garyStofer/wifi_wx_station/Hardware/Wifi_WX_Station/SPICE/rc-rc.asc

AC1: voltage; SINE(0 5 1.720K 0 0 0 300)
C1: cap; 1µf; V=10 Irms=11.456 Rser=0.004 Lser=0
C2: cap; 0.1µf
C3: cap; 1µf
R1: res; 8.2k; pwr=0.125
R2: res; 26.1k
R3: res; 8.2k
R4: res; 6.8K
Named nets: 0, out, vin, tap
.tran 400ms
.meas vmax MAX v(out) From 0.14 to 0.15
Use "View/Spice Error Log" to view the results of the .meas directive , or Ctrl-L
.meas vtap MAX v(tap) From 0.14 to 0.150
R3 and C2 is on Base station PCB
