garyStofer/wifi_wx_station/Hardware/Wifi_WX_Station/WindDir_WE28_A.1/Spice/IWind_encoder.asc

R4: res; 24.3k
R5: res; 14.3k
R6: res; 150k
R8: res; 100k
U2: opamp
V1: voltage; PULSE(0.33 2.97 00.1ms 10ms 75ns 100us 5.6ms 1)
V2: voltage; 3.3
Named nets: 0
.LIB opamp.sub
.tran 12ms
