garyStofer/wifi_wx_station/Hardware/Wifi_WX_Station/BMP085_HIH6130.brd

## EAGLE design Hardware/Wifi_WX_Station/BMP085_HIH6130.brd (2013-12-26)

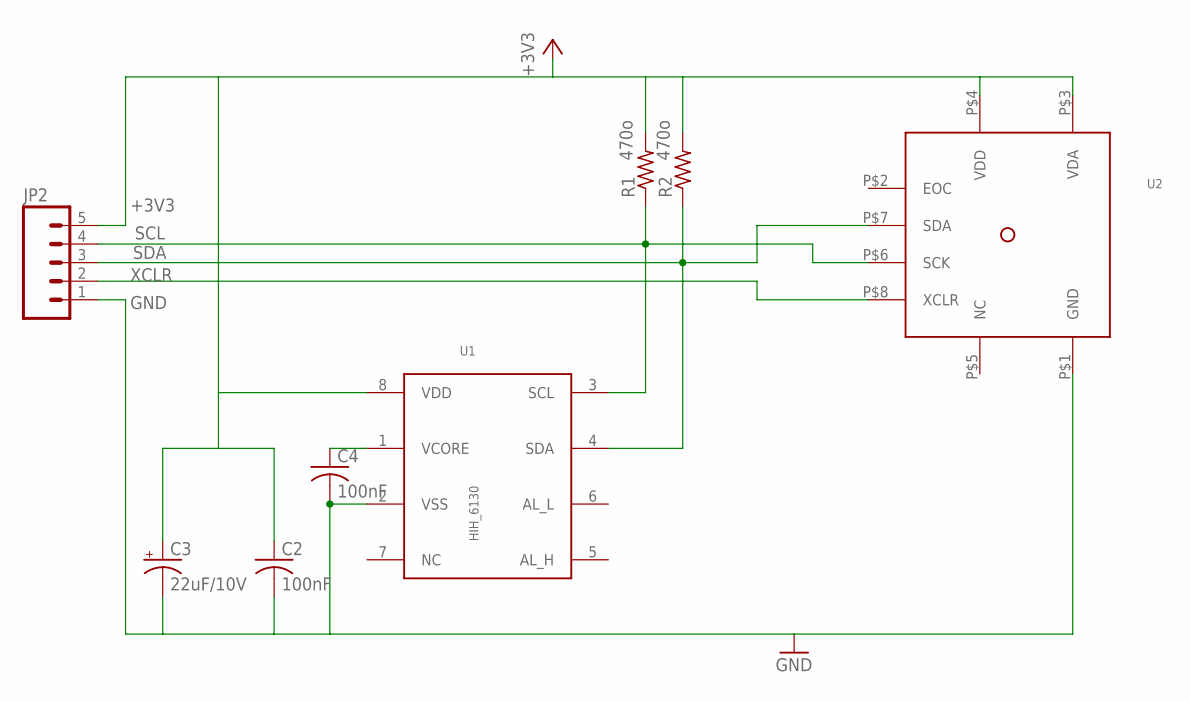
[picture p32: schematic BMP085_HIH6130.sch]

Parts:
C2, C4: 100nF; C0805K
C3: 22uF/10V; SMC_B
JP2: M05PTH; 1X05
R1, R2: 470o; R0603
U1: HIH_6130; SOIC8
U2: BMP085; LCC8

Connections:
+3V3: C2.1, C3.+, JP2.5, R1.2, R2.2, U1.8 (VDD), U2.P$3 (VDA), U2.P$4 (VDD)
GND: C2.2, C3.-, C4.2, JP2.1, U1.2 (VSS), U2.P$1 (GND)
unnamed: C4.1, U1.1 (VCORE)
SCL: JP2.4, R1.1, U1.3 (SCL), U2.P$6 (SCK)
SDA: JP2.3, R2.1, U1.4 (SDA), U2.P$7 (SDA)
XCLR: JP2.2, U2.P$8 (XCLR)

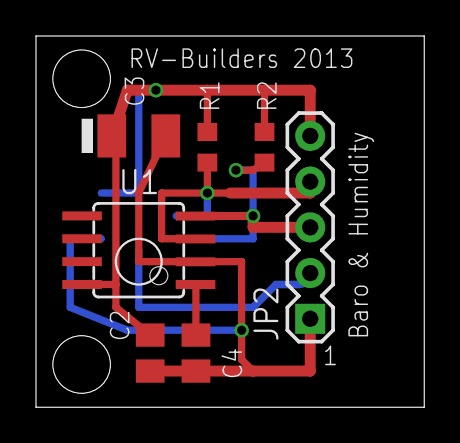
[picture p33: board BMP085_HIH6130.brd from above]

Board: 2 copper layers, 21.6 x 20.6 mm, 8 parts (1 on the bottom side), 6 nets.
