garyStofer/wifi_wx_station/Hardware/Wifi_WX_Station/Wind_enc.brd

## EAGLE design Hardware/Wifi_WX_Station/Wind_enc.brd (2013-11-12)

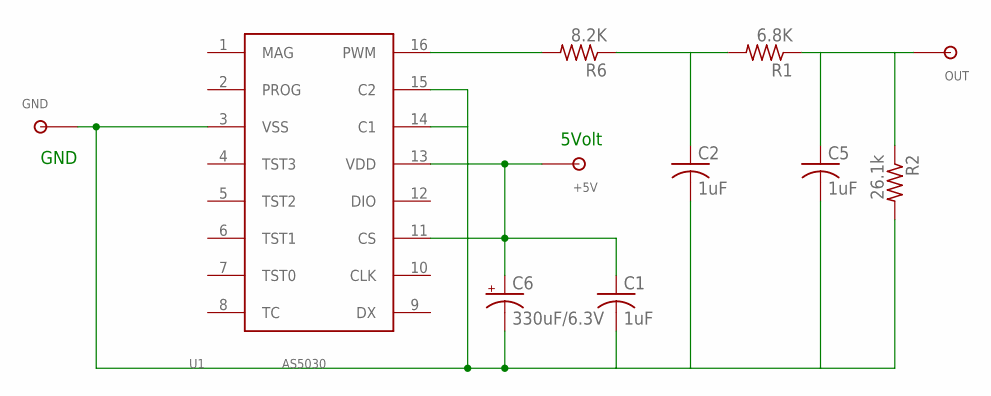
[picture p34: schematic Wind_enc.sch]

Parts:
+5V: TPSOL; TP_SOL
C1, C2, C5: 1uF; C0805K
C6: 330uF/6.3V; SMC_D
GND: TPSOL; TP_SOL
OUT: TPSOL; TP_SOL
R1: 6.8K; R0603
R2: 26.1k; R0603
R6: 8.2K; R0603
U1: AS5030; TSSOP16

Connections:
unnamed: +5V.P$1, C1.1, C6.+, U1.11 (CS), U1.13 (VDD)
unnamed: C1.2, C2.2, C5.2, C6.-, GND.P$1, R2.2, U1.3 (VSS), U1.14 (C1), U1.15 (C2)
unnamed: C5.1, OUT.P$1, R1.1, R2.1
unnamed: C2.1, R1.2, R6.1
unnamed: R6.2, U1.16 (PWM)

Notes on the sheet:
5Volt
GND

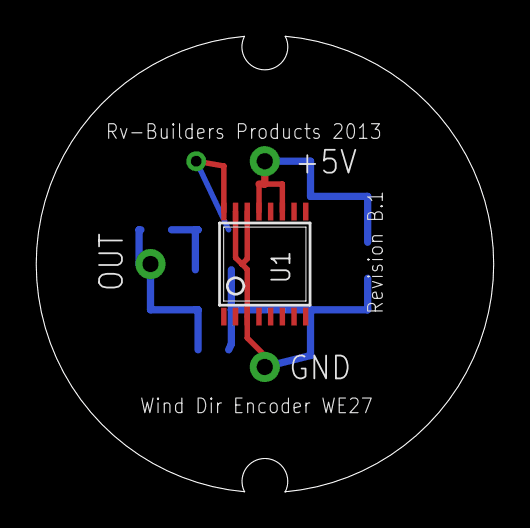
[picture p35: board Wind_enc.brd from above]

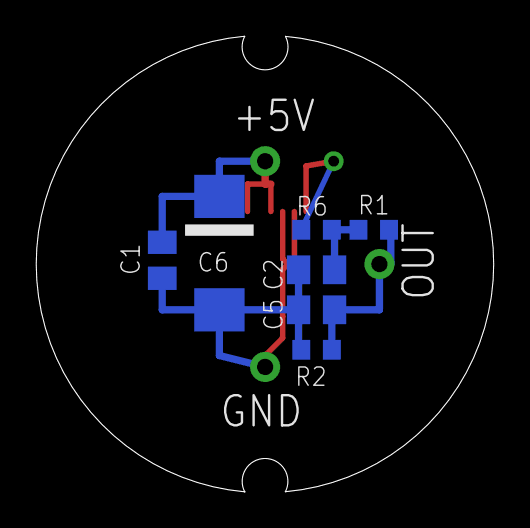
[picture p36: board Wind_enc.brd from below]

Board: 2 copper layers, 25.4 x 25.3 mm, 11 parts (7 on the bottom side), 5 nets.
