garyStofer/wifi_wx_station/Hardware/Wifi_WX_Station/VPower_feed.brd

## EAGLE design Hardware/Wifi_WX_Station/VPower_feed.brd (2013-03-08)

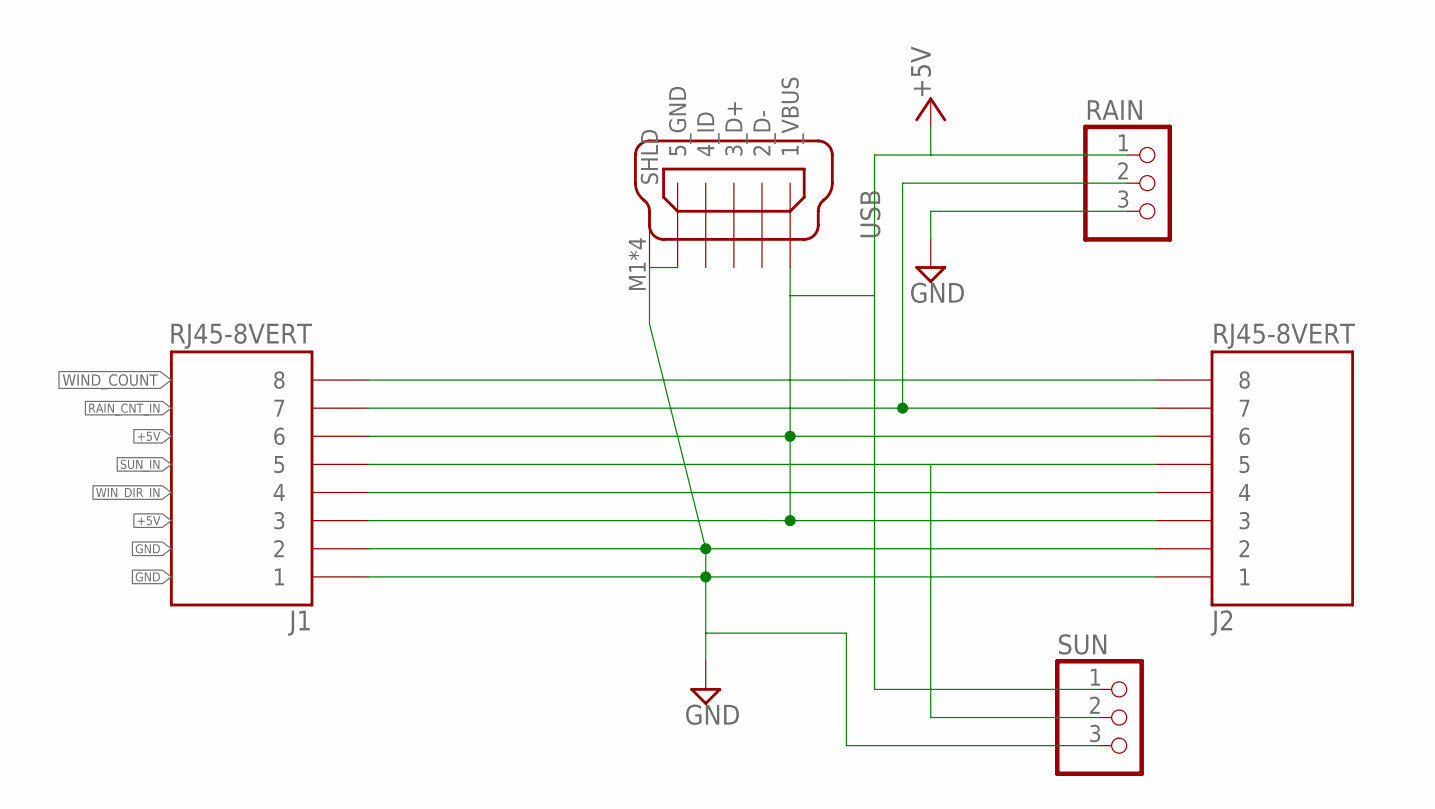
[picture p37: schematic VPower_feed.sch]

Parts:
J1, J2: RJ45-8VERT; RJ45_VERT
RAIN: PINHD-1X3MOLEX_KK; 1X3_MOLEX_KK
SUN: PINHD-1X3MOLEX_KK; 1X3_MOLEX_KK
USB: MINI-USB-32005-301; 32005-301

Connections:
+5V: J1.P$3 (3), J1.P$6 (6), J2.P$3 (3), J2.P$6 (6), RAIN.1, SUN.1, USB.1_VBUS
GND: J1.P$1 (1), J1.P$2 (2), J2.P$1 (1), J2.P$2 (2), RAIN.3, SUN.3, USB.5_USB_GND (5_GND), USB.M1 (SHLD), USB.M2 (SHLD), USB.M3 (SHLD), USB.M4 (SHLD)
RAIN_CNT_IN: J1.P$7 (7), J2.P$7 (7), RAIN.2
SUN_IN: J1.P$5 (5), J2.P$5 (5), SUN.2
WIND_COUNT: J1.P$8 (8), J2.P$8 (8)
WIN_DIR_IN: J1.P$4 (4), J2.P$4 (4)

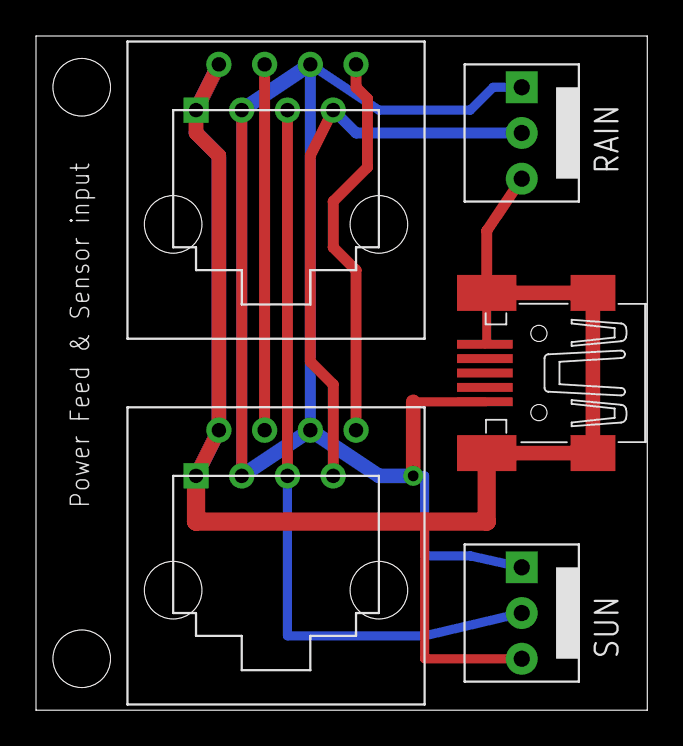
[picture p38: board VPower_feed.brd from above]

Board: 2 copper layers, 34.0 x 37.5 mm, 5 parts (0 on the bottom side), 6 nets.
