garyStofer/wifi_wx_station/Hardware/Wifi_WX_Station/sol_sens.brd

## EAGLE design Hardware/Wifi_WX_Station/sol_sens.brd (2013-03-08)

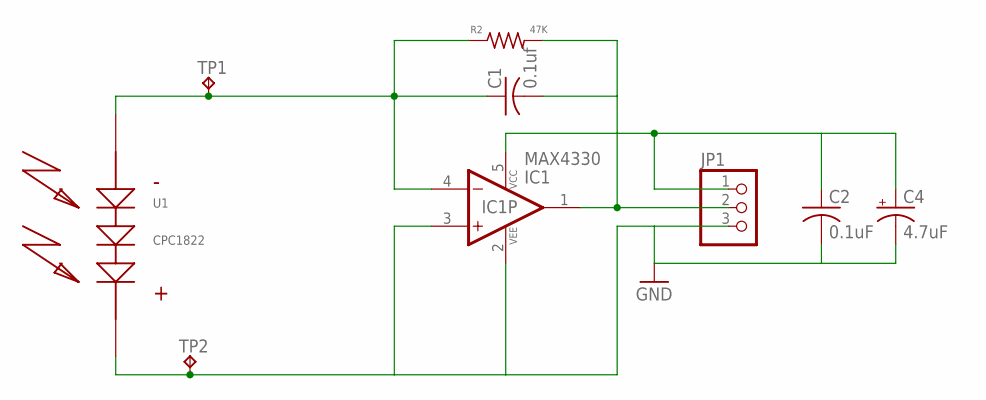
[picture p39: schematic sol_sens.sch]

Parts:
C1: 0.1uf; C0805
C2: 0.1uF; C0805
C4: 4.7uF; R/2012-12R
IC1: MAX4330; SOT23-5
JP1: PINHD-1X3; 1X03
R2: 47K; R0805
TP1, TP2: TPB1,27; B1,27
U1: CPC1822; SO08

Connections:
GND: C2.2, C4.-, IC1.2 (VEE), IC1.3 (+IN), JP1.3, TP2.PP, U1.8 (V+)
unnamed: C1.1, IC1.4 (-IN), R2.1, TP1.PP, U1.5 (V-)
unnamed: C1.2, IC1.1 (OUT), JP1.2, R2.2
unnamed: C2.1, C4.+, IC1.5 (VCC), JP1.1

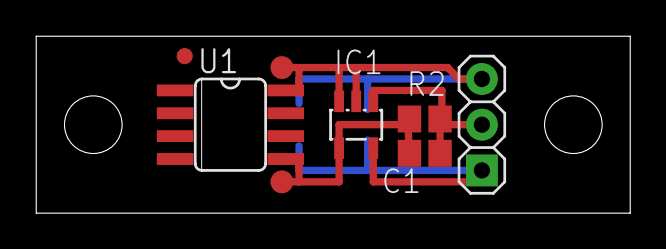
[picture p40: board sol_sens.brd from above]

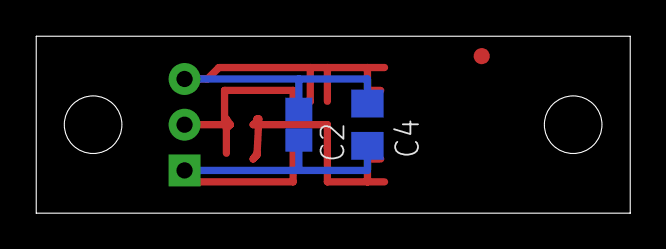
[picture p41: board sol_sens.brd from below]

Board: 2 copper layers, 33.0 x 9.8 mm, 9 parts (2 on the bottom side), 4 nets.
