garyStofer/wifi_wx_station/Hardware/Wifi_WX_Station/HP03S_HIH6130.brd

## EAGLE design Hardware/Wifi_WX_Station/HP03S_HIH6130.brd (2013-03-04)

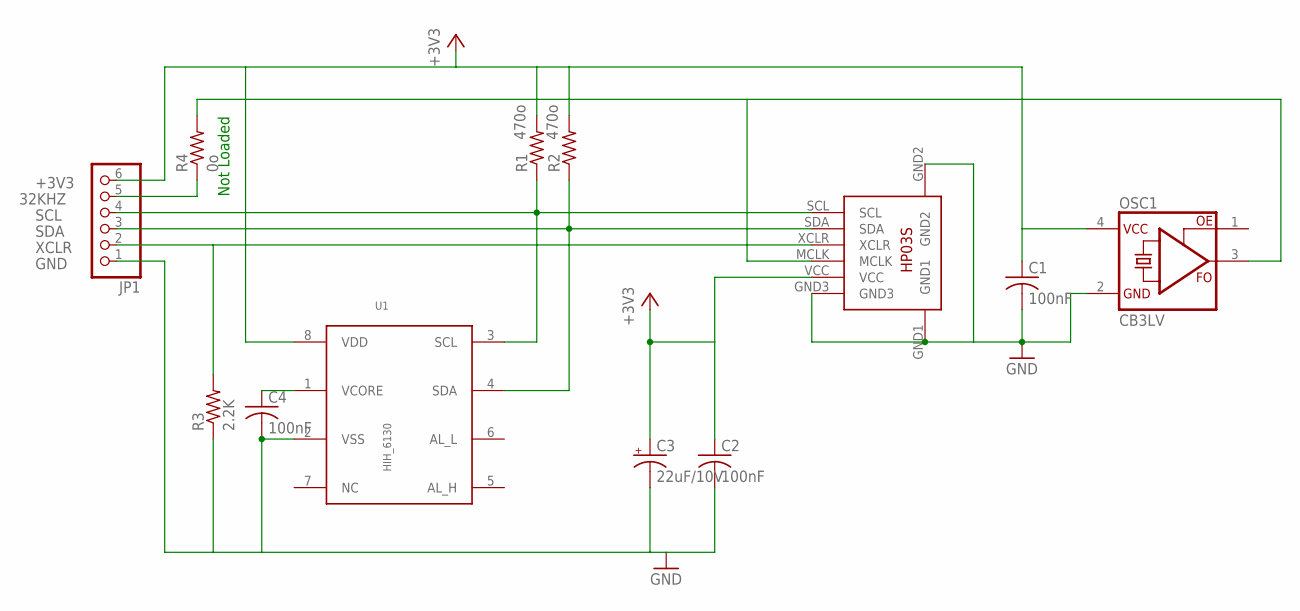
[picture p42: schematic HP03S_HIH6130.sch]

Parts:
C1: 100nF; C0805
C2, C4: 100nF; C0805K
C3: 22uF/10V; SMC_B
JP1: PINHD-1X6; 1X06
OSC1: CB3LV; SMD7.5X5MM
R1, R2: 470o; R0603
R3: 2.2K; R0603
R4: 0o; R0603
U1: HIH_6130; SOIC8
U2: HP03S

Connections:
32KHZ: JP1.5, R4.1
+3V3: C1.1, C2.1, C3.+, JP1.6, OSC1.4 (VCC), R1.2, R2.2, U1.8 (VDD), U2.VCC
GND: C1.2, C2.2, C3.-, C4.2, JP1.1, OSC1.2 (GND), R3.1, U1.2 (VSS), U2.GND1, U2.GND2, U2.GND3
unnamed: C4.1, U1.1 (VCORE)
RTCCLK: OSC1.3 (FO), R4.2, U2.MCLK
SCL: JP1.4, R1.1, U1.3 (SCL), U2.SCL
SDA: JP1.3, R2.1, U1.4 (SDA), U2.SDA
XCLR: JP1.2, R3.2, U2.XCLR

Notes on the sheet:
Not Loaded

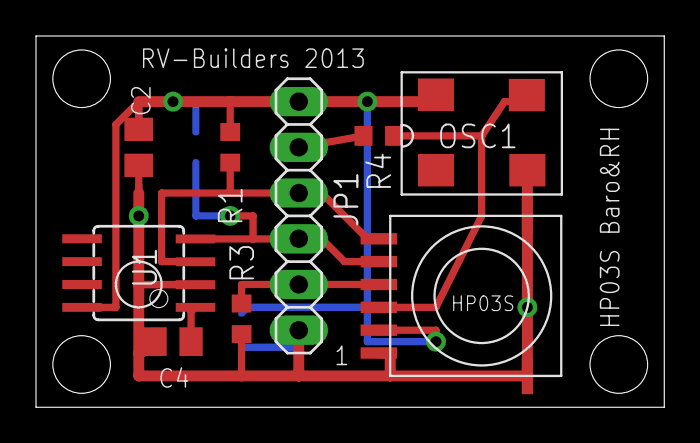
[picture p43: board HP03S_HIH6130.brd from above]

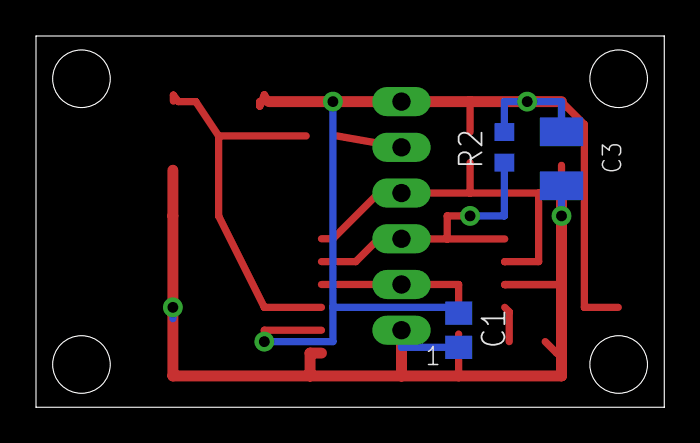
[picture p44: board HP03S_HIH6130.brd from below]

Board: 2 copper layers, 34.9 x 20.6 mm, 12 parts (3 on the bottom side), 8 nets.
