garyStofer/wifi_wx_station/Firmware/TCPIP/WiFi/WFMac_24G.c

/******************************************************************************

 MRF24W Driver Medium Access Control (MAC) Layer
 Module for Microchip TCP/IP Stack
  -Provides access to MRF24W WiFi controller
  -Reference: MRF24W Data sheet, IEEE 802.11 Standard

*******************************************************************************
 FileName:		WFMac.c
 Dependencies:	TCP/IP Stack header files
 Processor:		PIC18, PIC24F, PIC24H, dsPIC30F, dsPIC33F, PIC32
 Compiler:		Microchip C32 v1.10b or higher
				Microchip C30 v3.22 or higher
				Microchip C18 v3.34 or higher
 Company:		Microchip Technology, Inc.

 Software License Agreement

 Copyright (C) 2002-2010 Microchip Technology Inc.  All rights reserved.

 Microchip licenses to you the right to use, modify, copy, and distribute:
 (i)  the Software when embedded on a Microchip microcontroller or digital 
      signal controller product ("Device") which is integrated into 
      Licensee's product; or
 (ii) ONLY the Software driver source files ENC28J60.c, ENC28J60.h,
      ENCX24J600.c and ENCX24J600.h ported to a non-Microchip device used in 
	  conjunction with a Microchip ethernet controller for the sole purpose 
	  of interfacing with the ethernet controller.

 You should refer to the license agreement accompanying this Software for 
 additional information regarding your rights and obligations.

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

 Author				Date		Comment
~~~~~~~~~~~~~~~~~~~~~~~~~~~~~~~~~~~~~~~~~~~~~~~~~~~~~~~~~~~~~~~~~~~~~~~~~~~~~~~
 Michael Palladino	10/13/07	Original
 KO					31 Oct 2008	Port to PIC24F and PIC32 for TCP/IP stack v4.52
 KH					19 Jun 2009	Modified MACMemCopyAsync to support TCB to TCB copy
******************************************************************************/

/*
*********************************************************************************************************
*                                           INCLUDES                               
*********************************************************************************************************
*/

#include "TCPIP Stack/WFMac.h"

#if defined(WF_CS_TRIS) 

#include "TCPIP Stack/TCPIP.h"

#if defined( WF_CONSOLE )
#include "TCPIP Stack/WFConsole.h"
#include "IperfApp.h"
#endif 


#if defined(STACK_USE_UART)
extern void WF_OutputConnectionContext(void);
extern void ValidateConfig(void);
#endif

/*
*********************************************************************************************************
*                                           DEFINES                               
*********************************************************************************************************
*/

/* used for assertions */
#if defined(WF_DEBUG)
    #define WF_MODULE_NUMBER   WF_MODULE_WF_MAC
#endif

#define SNAP_VAL        (0xaa)
#define SNAP_CTRL_VAL   (0x03)
#define SNAP_TYPE_VAL   (0x00)

#define ETHER_IP        (0x00)
#define ETHER_ARP       (0x06)

#if defined( __PIC32MX__ )   
    #define IPL_MASK  ((UINT32)0x3f << 10)
#endif

#define SNAP_SIZE (6)

#define ENC_PREAMBLE_SIZE    (sizeof(ENC_PREAMBLE))
#define ENC_PREAMBLE_OFFSET  (10)

#define WF_RX_PREAMBLE_SIZE   (sizeof(tWFRxPreamble))
#define WF_TX_PREAMBLE_OFFSET (0)

#define WF_TX_PREAMBLE_SIZE   (sizeof(tWFTxPreamble))

#define MCHP_DATA_PACKET_SIZE (4 + MAX_PACKET_SIZE + 4)

#define RETRIEVE_BINARY_KEY       defined(WF_CONSOLE_DEMO)                                  \
                                                          &&                                                    \
                                  (MY_DEFAULT_WIFI_SECURITY_MODE == WF_SECURITY_WPA_WITH_PASS_PHRASE)     ||    \
                                  (MY_DEFAULT_WIFI_SECURITY_MODE == WF_SECURITY_WPA2_WITH_PASS_PHRASE)    ||    \
                                  (MY_DEFAULT_WIFI_SECURITY_MODE == WF_SECURITY_WPA_AUTO_WITH_PASS_PHRASE)
  



//============================================================================
//                                  Rx/Tx Buffer Constants
// Used to correlate former Ethernet packets to MRF24W packets.
//============================================================================
#define ENC_RX_BUF_TO_RAW_RX_BUF_ADJUSTMENT          ((RXSTART + ENC_PREAMBLE_SIZE)   - (ENC_PREAMBLE_OFFSET   + WF_RX_PREAMBLE_SIZE))
#define ENC_TX_BUF_TO_RAW_TX_BUF_ADJUSTMENT          ((TXSTART + WF_TX_PREAMBLE_SIZE) - (WF_TX_PREAMBLE_OFFSET + WF_TX_PREAMBLE_SIZE))
#define ENC_TCB_BUF_TO_RAW_SCRATCH_BUF_ADJUSTMENT    (BASE_TCB_ADDR)

//============================================================================
//                                  RAW Constants
//============================================================================
#define ENC_RD_PTR_ID               (0)
#define ENC_WT_PTR_ID               (1)


/*
*********************************************************************************************************
*                                           LOCAL MACROS                               
*********************************************************************************************************
*/


/*
*********************************************************************************************************
*                                           LOCAL DATA TYPES                               
*********************************************************************************************************
*/

#if defined( WF_CONSOLE_IFCFGUTIL )
extern tWFHibernate WF_hibernate;
#endif

typedef struct
{
    UINT8 type;
    UINT8 subType;
} tRxPreamble;

/* A header appended at the start of all RX frames by the hardware */
typedef struct _ENC_PREAMBLE
{
    WORD            NextPacketPointer;
    RXSTATUS        StatusVector;
    MAC_ADDR        DestMACAddr;
    MAC_ADDR        SourceMACAddr;
    WORD_VAL        Type;
} ENC_PREAMBLE;

typedef struct
{
    UINT8           snap[SNAP_SIZE];
    MAC_ADDR        DestMACAddr;
    MAC_ADDR        SourceMACAddr;
    WORD_VAL        Type;
} tWFRxPreamble;


typedef struct
{
    UINT8  reserved[4];
} tWFTxPreamble;


/*
*********************************************************************************************************
*                                           LOCAL GLOBAL VARIABLES                               
*********************************************************************************************************
*/

static UINT8  g_encPtrRAWId[2];  /* indexed by ENC_RD_PTR_ID (0) and ENC_WT_PTR_ID (1).  Values can be:           */
                                 /*   RAW_DATA_RX_ID, RAW_DATA_TX_ID, RAW_SCRATCH_ID                              */

/* keeps track of ENC read and write indexes */
static UINT16 g_encIndex[2];       /* index 0 stores current ENC read index, index 1 stores current ENC write index */

UINT16 g_rxBufferLength;
static UINT16 g_txPacketLength;
#if defined(WF_DEBUG)
static BOOL   g_txBufferFlushed;
#endif

/*
*********************************************************************************************************
*                                           LOCAL FUNCTION PROTOTYPES                               
*********************************************************************************************************
*/

static UINT16 MACIFService(void);
static void SyncENCPtrRAWState(UINT8 encPtrId, UINT16 encIndex);


#if defined ( WF_CONSOLE ) && defined ( EZ_CONFIG_SCAN ) && !defined(__18CXX)
extern void WFDisplayScanMgr();
#endif

UINT8 GetReadPtrRawWindow()
{
    return g_encPtrRAWId[ENC_RD_PTR_ID];
}

/*****************************************************************************
  Function:
	void SyncENCPtrRAWState(UINT8 encPtrId)

  Summary:
	Synchronizes the Ethernet RAM index to the WiFi RAW window index.

  Description:
	Any time stack code changes the index within the 'logical' Ethernet RAM
    this function must be called to assure the RAW driver is synced up with
    where the stack code thinks it is within the Ethernet RAM.  This applies
    to reading/writing tx data, rx data, or tcb data.  
    
    This function is typically called right after g_encIndex[] is updated.

  Precondition:
	None

  Parameters:
	encPtrId -- ENC_RD_PTR_ID or ENC_WT_PTR_ID
	             
  Returns:
  	None
  	
  Remarks:
	None
*****************************************************************************/
static void SyncENCPtrRAWState(UINT8 encPtrId, UINT16 encIndex)
{
    UINT8     rawId;
    UINT16    rawIndex;
    UINT32    startTickCount;
    UINT32    maxAllowedTicks;


    EnsureWFisAwake();
    
    /* Save the the read or write index value.  Code below will convert it to a */
    /* Raw index                                                                */
    g_encIndex[encPtrId] = encIndex;

    /*-----------------------------------------------------------------------------*/    
    /* if the input read or write pointer is in the Rx section of the Ethernet RAM */
    /*-----------------------------------------------------------------------------*/
    if (g_encIndex[encPtrId] < TXSTART)
    {
        /* set the rawId */
        rawId = RAW_DATA_RX_ID;

        /* Convert encPtr index to Raw Index */
        rawIndex = g_encIndex[encPtrId] - ENC_RX_BUF_TO_RAW_RX_BUF_ADJUSTMENT;

        // encPtr[encPtrId] < (RXSTART + ENC_PREAMBLE_SIZE) is an error since we don't have
        // the same preamble as the ENC chip
        WF_ASSERT( g_encIndex[encPtrId] >= (RXSTART + ENC_PREAMBLE_SIZE) );
        
    }
    /*----------------------------------------------------------------------------------*/    
    /* else if the input read or write pointer is in the Tx section of the Ethernet RAM */
    /*----------------------------------------------------------------------------------*/
    else if (g_encIndex[encPtrId] < BASE_TCB_ADDR)   
    {
        /* if the Tx data raw window has not yet been allocated (the stack is creating a new Tx data packet) */
        if (GetRawWindowState(RAW_DATA_TX_ID) != WF_RAW_DATA_MOUNTED)
        {
            /* WiFi chip may be in processs of transmitting a prior tx packet, so it is very possible that  */
            /* we won't be able to allocate a tx data packet instantly.  Set up timer and wait a reasonable */
            /* amount of time.                                                                              */
            maxAllowedTicks = TICKS_PER_SECOND * 6;  /* 6 second timeout, needed if scan in progress */
            startTickCount = (UINT32)TickGet();
            while ( !AllocateDataTxBuffer(MCHP_DATA_PACKET_SIZE) )
            {
        	    /* If timed out than lock up -- something bad happened */
                if (TickGet() - startTickCount >= maxAllowedTicks)
		        {
			        WF_ASSERT(FALSE);  /* timeout occurred */
		        }
            } 
        } 

        /* set the rawId */
        rawId = RAW_DATA_TX_ID;

        /* convert enc Ptr index to raw index */
        rawIndex = g_encIndex[encPtrId] - ENC_TX_BUF_TO_RAW_TX_BUF_ADJUSTMENT;

        /* encPtr[encPtrId] < BASE_TX_ADDR is an error since we don't have the same  */
        /* pre-BASE_TX_ADDR or post tx buffer as the ENC chip                        */
        WF_ASSERT((g_encIndex[encPtrId] >= BASE_TX_ADDR) && (g_encIndex[encPtrId] <= (BASE_TX_ADDR + MAX_PACKET_SIZE)));
    }
    /*----------------------------------------------------------------------------------*/    
    /* else input read or write pointer is in the TCB (Scratch) section of Ethernet RAM */
    /*----------------------------------------------------------------------------------*/
    else
    {
        /* set the raw Id, scratch is always mounted during intialization */
        rawId = RAW_SCRATCH_ID;

        /* convert Enc ptr index to raw index */
        rawIndex = g_encIndex[encPtrId] - ENC_TCB_BUF_TO_RAW_SCRATCH_BUF_ADJUSTMENT;
    }        
   
    /* set the raw index in the specified raw window */
    RawSetIndex(rawId, rawIndex);

    /* Update state variable so we know which raw window is being indexed by the read or write index.  */
    /* Will be either RAW_DATA_RX_ID, RAW_DATA_TX_ID, or RAW_SCRATCH_ID.                               */
    g_encPtrRAWId[encPtrId] = rawId;
    
}


#if defined(STACK_CLIENT_MODE) && defined(USE_GRATUITOUS_ARP)
//following is the workaround algorithm for the 11Mbps broadcast bugfix
extern BOOL ARPSendPkt(DWORD SrcIPAddr, DWORD DestIPAddr, BYTE op_req );
int WFArpBroadcastIntervalSec = 5; //interval in seconds, default to 5, can be changed
/*****************************************************************************
 * FUNCTION: WFPeriodicGratuitousArp
 *
 * RETURNS: None
 *
 * PARAMS:
 *          None
 *
 *  NOTES: this is a workaround algorithm for a bug appearing on some APs: they broadcasts
		   ARP Request over basic rate at 11Mpbs, that leaves our devices in dark. Here
		   we do ARP Request in the beginning for all the memebers in the subnet, then 
		   periodically do Gratuitous ARP to keep ourselves alive with the AP
 *****************************************************************************/
void WFPeriodicGratuitousArp(void)
{
	static DWORD oldTime = 0, currTime;
	static BYTE op_req = ARP_OPERATION_REQ;

    if (!MACIsLinked())
    {
        return;
    }    

	currTime = TickGet();
	
	if ( (currTime < oldTime) //wrap-around case
			||
		 ((currTime - oldTime) > WFArpBroadcastIntervalSec*TICK_SECOND)
		)
	{
        op_req = op_req == ARP_OPERATION_REQ ? ARP_OPERATION_RESP : ARP_OPERATION_REQ;
		ARPSendPkt(*(DWORD *)&AppConfig.MyIPAddr, *(DWORD *)&AppConfig.MyIPAddr, op_req );	
		oldTime = currTime;
	}
}
#endif //defined(STACK_CLIENT_MODE) && defined(USE_GRATUITOUS_ARP)

#if defined(SAVE_WPS_CONFIDENTIALS)
enum {
	AUTH_OPEN		= 0x01,
	AUTH_WPA_PSK	= 0x02,
	AUTH_SHARED 	= 0x04,
	AUTH_WPA		= 0x08,
	AUTH_WPA2		= 0x10,
	AUTH_WPA2_PSK	= 0x20	
};
	
enum {
	ENC_NONE		= 0x01,
	ENC_WEP 		= 0x02,
	ENC_TKIP		= 0x04,
	ENC_AES 		= 0x08
};

enum {
	WEP_SHORT_KEY_SIZE	= 5,
	WEP_LONG_KEY_SIZE	= 13
};

enum {
    SECURITY_NONE,
    SECURITY_OPEN,
    SECURITY_SHARED_KEY40,
    SECURITY_SHARED_KEY104,
    SECURITY_OPEN_KEY40,
    SECURITY_OPEN_KEY104,
    SECURITY_WPA1_PSK_KEY,
    SECURITY_WPA1_PSK_PASS,
    SECURITY_WPA2_PSK_KEY,
    SECURITY_WPA2_PSK_PASS,
    SECURITY_WPAUTO_PSK_KEY,
    SECURITY_WPAUTO_PSK_PASS,
    SECURITY_WPA_ENTERPRISE,
    SECURITY_WPS_PIN,
    SECURITY_WPS_PSB,
};

enum {
    WEP_KEYIDX_MAX = 4,
    MSK_MAX = 64,
    PIN_MAX = 8,
};

struct sec_wep40 {
    UINT8 key_idx;
    UINT8 key[WEP_KEYIDX_MAX][5];
};

struct sec_wep104 {
    UINT8 key_idx;
    UINT8 key[WEP_KEYIDX_MAX][13];
};

struct sec_wpa_psk {
    UINT8 key_len;
    UINT8 key[MSK_MAX];
};

struct sec_wps {
    UINT8 pin[PIN_MAX];
};

union sec_key {
    struct sec_wep40 wep40;
    struct sec_wep104 wep104;
    struct sec_wpa_psk wpa_psk;
    struct sec_wps wps;
};

#define SHORTSWAP(s) ((((s) >> 8) & 0xff) | (((s) << 8) & 0xff00))
#define LONGSWAP(l) ((((l) >> 24) & 0xff) | (((l) >> 8) & 0xff00) | (((l) << 8) & 0xff0000) | (((l) << 24) & 0xff000000))

static UINT8
ConvAscii2Hex(UINT8 a)
{
	if (a >= '0' && a <= '9')
		return (UINT8)(a - 48);
	if (a >= 'a' && a <= 'f')
		return (UINT8)(a - 97 + 10);
	if (a >= 'A' && a <= 'F')
		return (UINT8)(a - 65 + 10);

	return '?';
}

static void
ConvAsciiKey2Hex(UINT8 *key, UINT8 keyLen, UINT8 *hexKey)
{
	UINT8 i;

	for (i = 0; i < keyLen; i += 2) {
		hexKey[i / 2] = ConvAscii2Hex(key[i]) << 4;
		hexKey[i / 2] |= ConvAscii2Hex(key[i + 1]);
	}
}

static void
ConfigWep(tWFWpsCred *cred, UINT8 *secType, union sec_key *key)
{
	UINT8 i;
	UINT8 wep_key[WEP_LONG_KEY_SIZE];
	struct sec_wep40 *wep_ctx = (struct sec_wep40 *)key;
	UINT8 *keys = (UINT8 *)wep_ctx + 1;
	UINT8 key_len;
	
	if (cred->keyLen == WEP_SHORT_KEY_SIZE * 2) {
		*secType =	WF_SECURITY_WEP_40;
		ConvAsciiKey2Hex(cred->netKey, cred->keyLen, wep_key);
		key_len = cred->keyLen / 2;
	} else if (cred->keyLen == WEP_SHORT_KEY_SIZE) {
		*secType =	WF_SECURITY_WEP_40;
		memcpy(wep_key, cred->netKey, cred->keyLen);
		key_len = cred->keyLen;
	} else if (cred->keyLen == WEP_LONG_KEY_SIZE * 2) {
		*secType =	WF_SECURITY_WEP_104;
		ConvAsciiKey2Hex(cred->netKey, cred->keyLen, wep_key);
		key_len = cred->keyLen / 2;
	} else if (cred->keyLen == WEP_LONG_KEY_SIZE) {
		*secType = WF_SECURITY_WEP_104;
		memcpy(wep_key, cred->netKey, cred->keyLen);
		key_len = cred->keyLen;
	} else {
		WF_ASSERT(FALSE);
	}
	
	for (i = 0; i < 4; i++)
		memcpy(keys + i * key_len, wep_key, key_len);
				
	wep_ctx->key_idx = cred->keyIdx - 1;
}

static void 
WF_SaveWPSCredentials(UINT8 CpId)
{
	tWFWpsCred cred;
	union sec_key key;
	UINT8 *psk;
	static BOOL once = FALSE;

	if (!once) {
		WF_CPGetWPSCredentials(CpId, &cred);
		cred.authType = SHORTSWAP(cred.authType);
		cred.encType = SHORTSWAP(cred.encType);
		memcpy((void *)AppConfig.MySSID, (void *)cred.ssid, cred.ssidLen);
		AppConfig.SsidLength = cred.ssidLen;
		switch (cred.authType) {
		case AUTH_OPEN:
			if (cred.encType == ENC_NONE) {
				AppConfig.SecurityMode = WF_SECURITY_OPEN;
			} else if (cred.encType == ENC_WEP) {
				ConfigWep(&cred, &AppConfig.SecurityMode, &key);
				if (AppConfig.SecurityMode == WF_SECURITY_WEP_40) {
					memcpy((void *)AppConfig.SecurityKey, (void *)key.wep40.key, WEP_SHORT_KEY_SIZE * 4);
					AppConfig.SecurityKeyLength = WEP_SHORT_KEY_SIZE * 4;
					AppConfig.WepKeyIndex = key.wep40.key_idx;
				} else if (AppConfig.SecurityMode == WF_SECURITY_WEP_104) {
					memcpy((void *)AppConfig.SecurityKey, (void *)key.wep104.key, WEP_LONG_KEY_SIZE * 4);
					AppConfig.SecurityKeyLength = WEP_LONG_KEY_SIZE * 4;
					AppConfig.WepKeyIndex = key.wep104.key_idx;
				} else {
					WF_ASSERT(FALSE);
				}
			}
			break;
		case AUTH_SHARED:
			ConfigWep(&cred, &AppConfig.SecurityMode, &key);
			if (AppConfig.SecurityMode == WF_SECURITY_WEP_40) {
				memcpy((void *)AppConfig.SecurityKey, (void *)key.wep40.key, WEP_SHORT_KEY_SIZE * 4);
				AppConfig.SecurityKeyLength = WEP_SHORT_KEY_SIZE * 4;
				AppConfig.WepKeyIndex = key.wep40.key_idx;
			} else if (AppConfig.SecurityMode == WF_SECURITY_WEP_104) {
				memcpy((void *)AppConfig.SecurityKey, (void *)key.wep104.key, WEP_LONG_KEY_SIZE * 4);
				AppConfig.SecurityKeyLength = WEP_LONG_KEY_SIZE * 4;
				AppConfig.WepKeyIndex = key.wep104.key_idx;
			} else {
				WF_ASSERT(FALSE);
			}
			break;
		case AUTH_WPA_PSK:
		case AUTH_WPA2_PSK:
			psk = (UINT8 *)AppConfig.SecurityKey;
			memset((void *)psk, 0x00, 64);
			if (cred.keyLen == 64) {
				AppConfig.SecurityMode = cred.authType == AUTH_WPA_PSK ?
					WF_SECURITY_WPA_WITH_KEY : WF_SECURITY_WPA2_WITH_KEY;
				AppConfig.SecurityKeyLength = 32;
				ConvAsciiKey2Hex(cred.netKey, cred.keyLen, psk);
			} else if (cred.keyLen >= 8 && cred.keyLen < 64) {
				AppConfig.SecurityMode = cred.authType == AUTH_WPA_PSK ?
					WF_SECURITY_WPA_WITH_PASS_PHRASE : WF_SECURITY_WPA2_WITH_PASS_PHRASE;
				AppConfig.SecurityKeyLength = cred.keyLen;
				if (AppConfig.SecurityKeyLength > 8 
					&& cred.netKey[AppConfig.SecurityKeyLength - 1] == '\0')
					--AppConfig.SecurityKeyLength;
				memcpy(psk, cred.netKey, AppConfig.SecurityKeyLength);
			}
			break;
		default:
			WF_ASSERT(FALSE);
			break;
		}
		once = TRUE;
	}
}
#endif	/* #if defined(SAVE_WPS_CONFIDENTIALS) */

// if WPA Passphrase being used
#if RETRIEVE_BINARY_KEY == TRUE        
// Used when connected using a security pass-phrase.  After the 
// connection is successful, this code will retrieve the binary pass phrase and 
// update AppConfig with it.  It will also change AppConfig.SecurityMode to use
// the binary key for future connections, specifically after a hibernate and wakeup.
// This avoids having to wait 30 seconds or so for the MRF24WG to recacalculate the key.
void RetrieveBinaryKey(UINT8 cpid)
{
    UINT8 securityType;
    UINT8 wepKeyIndex;
      
    /* copy binary key into AppConfig */
    WF_CPGetSecurity(cpid, &securityType, &wepKeyIndex, AppConfig.SecurityKey, &AppConfig.SecurityKeyLength);
    #if (MY_DEFAULT_WIFI_SECURITY_MODE == WF_SECURITY_WPA_WITH_PASS_PHRASE)
        AppConfig.SecurityMode = WF_SECURITY_WPA_WITH_KEY;
    #elif (MY_DEFAULT_WIFI_SECURITY_MODE == WF_SECURITY_WPA2_WITH_PASS_PHRASE)
        AppConfig.SecurityMode = WF_SECURITY_WPA2_WITH_KEY;
    #else
        AppConfig.SecurityMode = WF_SECURITY_WPA_AUTO_WITH_KEY;
    #endif                                 
}          
#endif /* RETRIEVE_BINARY_KEY == TRUE */  

#if defined(WF_USE_POWER_SAVE_FUNCTIONS)
static void CheckHibernate(void)
{
    #if defined( WF_CONSOLE_IFCFGUTIL )
    UINT8 state, cpid;
    #endif
    
    #if defined( WF_CONSOLE_IFCFGUTIL )
     	if (WF_hibernate.wakeup_notice && (WF_hibernate.state == WF_HB_WAIT_WAKEUP)) 
     	{
    	    DelayMs(200);
    
    		WF_hibernate.state = WF_HB_NO_SLEEP;
    		StackInit();
        	#if defined(WF_CONSOLE_DEMO)
    		IperfAppInit();
    		#endif
    
    		WF_Connect();
    	}
    #endif

	
    #if defined( WF_CONSOLE_IFCFGUTIL )
       wait_console_input:
    #endif
        
    #if defined(WF_CONSOLE) 
		WFConsoleProcess();
		#if defined( WF_CONSOLE_DEMO )
    		if (WF_hibernate.state == WF_HB_NO_SLEEP)
    		{
    			IperfAppCall();
    		}	
       		WFConsoleProcessEpilogue();
	    #endif
	#endif


	#if defined( WF_CONSOLE_IFCFGUTIL )
		if (WF_hibernate.state != WF_HB_NO_SLEEP) 
    	{
			if (WF_hibernate.state == WF_HB_ENTER_SLEEP) 
    		{
        		// if we are connected then disconnect before going into hibernate state
        		WF_CMGetConnectionState(&state, &cpid);
        		if ((state == WF_CSTATE_CONNECTED_INFRASTRUCTURE) || (state == WF_CSTATE_CONNECTED_ADHOC))
        		{
            		WF_CMDisconnect();
                }  		

			    WF_HibernateEnable();
				WF_hibernate.state = WF_HB_WAIT_WAKEUP;
			}
			if (WF_hibernate.wakeup_notice) 
			{
				//continue;
			}	
			else
			{
				goto wait_console_input;
            }				
		}
	#endif	    
} 
#endif /* WF_USE_POWER_SAVE_FUNCTIONS */   

/*****************************************************************************
 * FUNCTION: MACProcess
 *
 * RETURNS: None
 *
 * PARAMS:
 *          None
 *
 *  NOTES: Called form main loop to support 802.11 operations
 *****************************************************************************/
void MACProcess(void)
{
	static BOOL oneTimeJobDone = FALSE;
    /* Let 802.11 processes have a chance to run */
    WFProcess();

	if (MACIsLinked()) {
		if (!oneTimeJobDone) {
   	   		#if defined(STACK_USE_UART) && defined(MRF24WG)
        	WF_OutputConnectionContext(); 
    		#endif
    
    		// Retrieves binary key if we connected with WPA passphrase and changes AppConfig so we will
    		// use the binary key to reconnect
    		#if RETRIEVE_BINARY_KEY == TRUE
        	RetrieveBinaryKey(1);
    		#endif
	
			#if defined(SAVE_WPS_CONFIDENTIALS)
			WF_SaveWPSCredentials(1);
			#endif	/* defined(SAVE_WPS_CONFIDENTIALS) */
			
			oneTimeJobDone = TRUE;
		}
	} else {
		oneTimeJobDone = FALSE;
	}

    // checks if going into or coming out of hibernate mode
    #if defined(WF_USE_POWER_SAVE_FUNCTIONS)    
    CheckHibernate();
    #endif    
    
    #if defined(STACK_CLIENT_MODE) && defined(USE_GRATUITOUS_ARP)
    	//following is the workaround algorithm for the 11Mbps broadcast bugfix
    	WFPeriodicGratuitousArp();
    #endif 	
}

 /******************************************************************************
 * Function:        void MACInit(void)
 *
 * PreCondition:    None
 *
 * Input:           None
 *
 * Output:          None
 *
 * Side Effects:    None
 *
 * Overview:        MACInit sets up the PIC's SPI module and all the
 *                  registers in the MRF24W so that normal operation can
 *                  begin.
 *
 * Note:            None
 *****************************************************************************/
void MACInit(void)
{
    #if defined(STACK_USE_UART)
    ValidateConfig();
    #endif
    
    WF_Init();
}

/******************************************************************************
 * Function:        void RawInit(void)
 *
 * PreCondition:    None
 *
 * Input:           None
 *
 * Output:          None
 *
 * Side Effects:    None
 *
 * Overview:        Initializes the RAW window states.
 *
 * Note:            None
 *****************************************************************************/
void RawInit(void)
{
    /* By default the firmware mounts Scratch to RAW 1 after reset.  If desired,    */
    /* we can read the SysInfo data block from the Scratch.  We are not using this  */
    /* data, so unmount the scratch from this RAW window.                           */
    ScratchUnmount(RAW_ID_1);

    /* Mount scratch memory, index defaults to 0.  This will stay permanently mounted.   */
    /* If one needs to know, this function returns the number of bytes in scratch memory */
    ScratchMount(RAW_SCRATCH_ID);
    
    g_encPtrRAWId[ENC_RD_PTR_ID] = RAW_DATA_RX_ID;
    g_encIndex[ENC_RD_PTR_ID]    = BASE_TCB_ADDR;

    SetRawWindowState(RAW_DATA_TX_ID, WF_RAW_UNMOUNTED);

    g_encPtrRAWId[ENC_WT_PTR_ID]  = RAW_DATA_TX_ID;
    g_encIndex[ENC_WT_PTR_ID]     = BASE_TX_ADDR;                 // set tx encode ptr (index) to start of tx buf + 4 bytes

    SetRxDataPacketLength(0);                                     // current rx buffer length (none) is 0 bytes
    g_txPacketLength  = 0;                                        // current tx packet length (none) is 0 bytes
    #if defined(WF_DEBUG)
    g_txBufferFlushed = TRUE;                                     // tx buffer is flushed
    #endif
    
    // from ENC MAC init
    // encWrPtr is left pointing to BASE_TX_ADDR
    // encRdPtr is not initialized... we leave it pointing to BASE_TCB_ADDR

    g_RawIndexPastEnd = 0x00; /* no raw indexes have been set past end of raw window */
}    




/******************************************************************************
 * Function:        BOOL MACIsLinked(void)
 *
 * PreCondition:    None
 *
 * Input:           None
 *
 * Output:          TRUE: If the PHY reports that a link partner is present
 *                        and the link has been up continuously since the last
 *                        call to MACIsLinked()
 *                  FALSE: If the PHY reports no link partner, or the link went
 *                         down momentarily since the last call to MACIsLinked()
 *
 * Side Effects:    None
 *
 * Overview:        Returns the PHSTAT1.LLSTAT bit.
 *
 * Note:            None
 *****************************************************************************/
BOOL MACIsLinked(void)
{
    return ( WFisConnected() );
}

/*****************************************************************************
  Function:
	BOOL MACIsTxReady(void))

  Summary:
	Checks if a tx data buffer is available on the WiFi chip.

  Description:
	Checks if a raw window is currently mounted.  If not, the tx data raw window
	is mounted.

  Precondition:
	MACInit must be called first.

  Parameters:
	None
	             
  Returns:
  	True if tx data buffer available, else false
  	
  Remarks:
	None
*****************************************************************************/
BOOL MACIsTxReady(void)
{
    BOOL result;

    /* if raw tx data window is in use */
    if (GetRawWindowState(RAW_DATA_TX_ID) == WF_RAW_DATA_MOUNTED)
    {
        result = TRUE;
    }    
    /* else raw tx data window is available */
    else
    {

        /* create the new tx buffer */
        result = AllocateDataTxBuffer(MCHP_DATA_PACKET_SIZE);
    }    

    return result;
}



void RawGetMgmtRxBuffer(UINT16 *p_numBytes)
{
    /* Mount the mgmt pool rx data, returns number of bytes in mgmt msg.  Read */
    /* index defaults to 0.                                                    */
    *p_numBytes = RawMountRxBuffer(RAW_MGMT_RX_ID);
}



/******************************************************************************
 * Function:        void MACDiscardRx(void)
 *
 * PreCondition:    None
 *
 * Input:           None
 *
 * Output:          None
 *
 * Side Effects:    None
 *
 * Overview:        Marks the last received packet (obtained using
 *                  MACGetHeader())as being processed and frees the buffer
 *                  memory associated with it
 *
 * Note:            It is safe to call this function multiple times between
 *                  MACGetHeader() calls.  Extra packets won't be thrown away
 *                  until MACGetHeader() makes it available.
 *****************************************************************************/
void MACDiscardRx(void)
{
    /* if we currently have a rx buffer mounted then deallocate it as stack no */
    /* longer needs it.                                                        */
    if ( GetRawWindowState(RAW_DATA_RX_ID) == WF_RAW_DATA_MOUNTED )
    {
        DeallocateDataRxBuffer();
    }
}


/******************************************************************************
 * Function:        WORD MACGetFreeRxSize(void)
 *
 * PreCondition:    None
 *
 * Input:           None
 *
 * Output:          A WORD estimate of how much RX buffer space is free at
 *                  the present time.
 *
 * Side Effects:    None
 *
 * Overview:        None
 *
 * Note:            None
 *****************************************************************************/
WORD MACGetFreeRxSize(void)
{
    WORD size;

    /* if no Rx packet is currently mounted */
    if ( GetRxDataPacketLength() == 0)
    {
        /* TCP/IP stack has entire Rx block available */
        size = RXSIZE - 1;
    }
    /* else a Rx data packet is currently mounted */
    else
    {
        if ( (RXSTOP - RXSTART) > GetRxDataPacketLength() )
        {
            size = (RXSTOP - RXSTART) - GetRxDataPacketLength();
        }
        else
        {
            size = 0;
        }
    }

    return size;
}

/*****************************************************************************
 * FUNCTION: MACIFService
 *
 *
 * RETURNS: Number of bytes in the Data Rx packet if one is received, else 0.
 *
 * PARAMS:  None
 *
 *  NOTES: Called by MACGetHeader() to see if any data packets have been received.
 *         If the MRF24W has received a data packet and the data packet is not
 *         a management data packet, then this function returns the number of
 *         bytes in the data packet. Otherwise it returns 0.
 *****************************************************************************/
static UINT16 MACIFService(void)
{
    UINT16 byteCount;
    tRxPreamble wfPreamble;

    /* check if external interrupt has signalled receipt of a data frame */
    if (!g_HostRAWDataPacketReceived)
    {
        byteCount = 0;  /* return 0 indicating no data rx frame received */
    }
    /* else external interrupt received indicating a data rx frame ready for TCP/IP stack */
    else
    {
        g_HostRAWDataPacketReceived = FALSE; /* clear flag for next data packet */
    
        /* Mount Read FIFO to RAW Rx window.  Allows use of RAW engine to read rx data packet. */
        /* Function call returns number of bytes in the data packet.                           */
        byteCount = RawMountRxBuffer(RAW_DATA_RX_ID);
        WF_ASSERT(byteCount > 0);  
        SetRxDataPacketLength(byteCount);
        
        /* now that buffer mounted it is safe to reenable interrupts, which were left disabled */
        /* in the WiFi interrupt handler.                                                      */
        WF_EintEnable();
    
        /* read the data frame internal preamble (type and subtype) to verify that we did, in   */
        /* fact, mount an Rx data packet.  This read auto-increments the raw index to the first */
        /* actual data byte in the frame.                                                       */
        RawGetByte(RAW_DATA_RX_ID, (UINT8*)&wfPreamble, sizeof(tRxPreamble));
        WF_ASSERT(wfPreamble.type == WF_DATA_RX_INDICATE_TYPE);
    }

    return byteCount;
}

 
/******************************************************************************
 * Function:        BOOL MACGetHeader(MAC_ADDR *remote, BYTE* type)
 *
 * PreCondition:    None
 *
 * Input:           *remote: Location to store the Source MAC address of the
 *                           received frame.
 *                  *type: Location of a BYTE to store the constant
 *                         MAC_UNKNOWN, ETHER_IP, or ETHER_ARP, representing
 *                         the contents of the Ethernet type field.
 *
 * Output:          TRUE: If a packet was waiting in the RX buffer.  The
 *                        remote, and type values are updated.
 *                  FALSE: If a packet was not pending.  remote and type are
 *                         not changed.
 *
 * Side Effects:    Last packet is discarded if MACDiscardRx() hasn't already
 *                  been called.
 *
 * Overview:        None
 *
 * Note:            None
 *****************************************************************************/
BOOL MACGetHeader(MAC_ADDR *remote, BYTE* type)
{
    UINT16 len;
    tWFRxPreamble header;
    
    /* stack no longer cares about currently mounted rx packet, so clear flag */
    ClearIndexOutOfBoundsFlag(RAW_DATA_RX_ID);

    /* if we currently have a rx buffer mounted then deallocate it as stack no */
    /* longer needs it.                                                        */
    if ( GetRawWindowState(RAW_DATA_RX_ID) == WF_RAW_DATA_MOUNTED )
    {
        DeallocateDataRxBuffer();
    }

    /* check WiFi chip to see if a data frame has been received.  If so, the length of the */
    /* data frame is returned. If no data packet received then 0 will be returned.         */
    len = MACIFService();
    if ( len == 0 )
    {
        return FALSE;
    }
    


    /* read preamble header.  The RAW index was left at index 2 in the call to MACIFService, which */
    /* is the logical start of the received data frame LLC Header, also known as the SNAP header.  */
    RawRead(RAW_DATA_RX_ID, ENC_PREAMBLE_OFFSET, WF_RX_PREAMBLE_SIZE, (UINT8 *)&header);  

    /* as a sanity check verify that the expected bytes contain the SNAP header */
    if (!(header.snap[0] == SNAP_VAL        && 
          header.snap[1] == SNAP_VAL        &&
          header.snap[2] == SNAP_CTRL_VAL   &&
          header.snap[3] == SNAP_TYPE_VAL   && 
          header.snap[4] == SNAP_TYPE_VAL   && 
          header.snap[5] == SNAP_TYPE_VAL) )
    {
        /* if a vendor proprietary packet, throw away */
        DeallocateDataRxBuffer();
        return FALSE;
    }
  

#if 0
/* this should no longer be needed */
    /* we can flush any saved RAW state now by saving and restoring the current rx buffer.  */
    PushRawWindow(RAW_DATA_RX_ID);
    PopRawWindow(RAW_DATA_RX_ID); 
#endif
    
    // set RAW pointer to 802.11 payload
    RawSetIndex(RAW_DATA_RX_ID, (ENC_PREAMBLE_OFFSET + WF_RX_PREAMBLE_SIZE));

    g_encPtrRAWId[ENC_RD_PTR_ID] = RAW_DATA_RX_ID;
    g_encIndex[ENC_RD_PTR_ID]    = RXSTART + sizeof(ENC_PREAMBLE);

    // The EtherType field, like most items transmitted on the Ethernet medium
    // are in big endian.
    header.Type.Val = swaps(header.Type.Val);

    // Return the Ethernet frame's Source MAC address field to the caller
    // This parameter is useful for replying to requests without requiring an
    // ARP cycle.
    memcpy((void*)remote->v, (void*)header.SourceMACAddr.v, sizeof(*remote));

    // Return a simplified version of the EtherType field to the caller
    *type = MAC_UNKNOWN;
    if( (header.Type.v[1] == 0x08u) &&
        ((header.Type.v[0] == ETHER_IP) || (header.Type.v[0] == ETHER_ARP)) )
    {
        *type = header.Type.v[0];
    }

    return TRUE;
}

/******************************************************************************
 * Function:        void MACPutHeader(MAC_ADDR *remote, BYTE type, WORD dataLen)
 *
 * PreCondition:    MACIsTxReady() must return TRUE.
 *
 * Input:           *remote: Pointer to memory which contains the destination
 *                           MAC address (6 bytes)
 *                  type: The constant ETHER_ARP or ETHER_IP, defining which
 *                        value to write into the Ethernet header's type field.
 *                  dataLen: Length of the Ethernet data payload
 *
 * Output:          None
 *
 * Side Effects:    None
 *
 * Overview:        None
 *
 * Note:            Because of the dataLen parameter, it is probably
 *                  advantagous to call this function immediately before
 *                  transmitting a packet rather than initially when the
 *                  packet is first created.  The order in which the packet
 *                  is constructed (header first or data first) is not
 *                  important.
 *****************************************************************************/
void MACPutHeader(MAC_ADDR *remote, BYTE type, WORD dataLen)
{
    UINT8 buf[14];
       
    #if defined(WF_DEBUG)
    g_txBufferFlushed = FALSE;
    #endif
    
    g_txPacketLength = dataLen + (WORD)sizeof(ETHER_HEADER) + WF_TX_PREAMBLE_SIZE;

    // Set the SPI write pointer to the beginning of the transmit buffer (post WF_TX_PREAMBLE_SIZE)
    SyncENCPtrRAWState(ENC_WT_PTR_ID, TXSTART + WF_TX_PREAMBLE_SIZE);

    /*  write the Ethernet destination address to buffer (6 bytes) */
    memcpy(&buf[0], (void *)remote, sizeof(*remote));
    /* write snap header to buffer (6 bytes) */
    buf[6] =  SNAP_VAL;         
    buf[7] =  SNAP_VAL;
    buf[8] =  SNAP_CTRL_VAL;
    buf[9] =  SNAP_TYPE_VAL;
    buf[10] = SNAP_TYPE_VAL;
    buf[11] = SNAP_TYPE_VAL;
    /* Write the appropriate Ethernet Type WORD for the protocol being used */
    buf[12] = 0x08;                 
    buf[13] = (type == MAC_IP) ? ETHER_IP : ETHER_ARP;

    /* write buffer to RAW window */
    MACPutArray((BYTE *)buf, sizeof(buf));
}



/******************************************************************************
 * Function:        void MACFlush(void)
 *
 * PreCondition:    A packet has been created by calling MACPut() and
 *                  MACPutHeader().
 *
 * Input:           None
 *
 * Output:          None
 *
 * Side Effects:    None
 *
 * Overview:        MACFlush causes the current TX packet to be sent out on
 *                  the Ethernet medium.  The hardware MAC will take control
 *                  and handle CRC generation, collision retransmission and
 *                  other details.
 *
 * Note:            After transmission completes (MACIsTxReady() returns TRUE),
 *                  the packet can be modified and transmitted again by calling
 *                  MACFlush() again.  Until MACPutHeader() or MACPut() is
 *                  called (in the TX data area), the data in the TX buffer
 *                  will not be corrupted.
 *****************************************************************************/
void MACFlush(void)
{
   
    /* this function should not be called after the current tx buffer has been transmitted */
    WF_ASSERT(!g_txBufferFlushed);

    #if defined(WF_DEBUG)
    g_txBufferFlushed = TRUE;
    #endif

    EnsureWFisAwake();
    SendRAWDataFrame(g_txPacketLength);
}


/******************************************************************************
 * Function:        void MACSetReadPtrInRx(WORD offset)
 *
 * PreCondition:    A packet has been obtained by calling MACGetHeader() and
 *                  getting a TRUE result.
 *
 * Input:           offset: WORD specifying how many bytes beyond the Ethernet
 *                          header's type field to relocate the SPI read
 *                          pointer.
 *
 * Output:          None
 *
 * Side Effects:    None
 *
 * Overview:        SPI read pointer are updated.  All calls to
 *                  MACGet() and MACGetArray() will use these new values.
 *
 * Note:            RXSTOP must be statically defined as being > RXSTART for
 *                  this function to work correctly.  In other words, do not
 *                  define an RX buffer which spans the 0x1FFF->0x0000 memory
 *                  boundary.
 *****************************************************************************/
void MACSetReadPtrInRx(WORD offset)
{
    SyncENCPtrRAWState(ENC_RD_PTR_ID, RXSTART + sizeof(ENC_PREAMBLE) + offset);
}


/******************************************************************************
 * Function:        WORD MACSetWritePtr(WORD Address)
 *
 * PreCondition:    None
 *
 * Input:           Address: Address to seek to
 *
 * Output:          WORD: Old EWRPT location
 *
 * Side Effects:    None
 *
 * Overview:        SPI write pointer is updated.  All calls to
 *                  MACPut() and MACPutArray() will use this new value.
 *
 * Note:            None
 *****************************************************************************/
PTR_BASE MACSetWritePtr(PTR_BASE address)
{
    PTR_BASE oldVal;

    oldVal = g_encIndex[ENC_WT_PTR_ID];

    SyncENCPtrRAWState(ENC_WT_PTR_ID, address);

    return oldVal;
}

/******************************************************************************
 * Function:        WORD MACSetReadPtr(WORD Address)
 *
 * PreCondition:    None
 *
 * Input:           Address: Address to seek to
 *
 * Output:          WORD: Old ERDPT value
 *
 * Side Effects:    None
 *
 * Overview:        SPI write pointer is updated.  All calls to
 *                  MACPut() and MACPutArray() will use this new value.
 *
 * Note:            None
 *****************************************************************************/
PTR_BASE MACSetReadPtr(PTR_BASE address)
{
    PTR_BASE oldVal;

    oldVal = g_encIndex[ENC_RD_PTR_ID];

    SyncENCPtrRAWState(ENC_RD_PTR_ID, address);

    return oldVal;
}


/******************************************************************************
 * Function:        WORD MACCalcRxChecksum(WORD offset, WORD len)
 *
 * PreCondition:    None
 *
 * Input:           offset  - Number of bytes beyond the beginning of the
 *                          Ethernet data (first byte after the type field)
 *                          where the checksum should begin
 *                  len     - Total number of bytes to include in the checksum
 *
 * Output:          16-bit checksum as defined by RFC 793.
 *
 * Side Effects:    None
 *
 * Overview:        This function performs a checksum calculation in the MAC
 *                  buffer itself
 *
 * Note:            None
 *****************************************************************************/
WORD MACCalcRxChecksum(WORD offset, WORD len)
{
    WORD temp;
    UINT16 rdSave;

    // Add the offset requested by firmware plus the Ethernet header
    temp = RXSTART + sizeof(ENC_PREAMBLE) + offset;

    rdSave = g_encIndex[ENC_RD_PTR_ID];

    SyncENCPtrRAWState(ENC_RD_PTR_ID, temp);

    temp = CalcIPBufferChecksum(len);

    SyncENCPtrRAWState(ENC_RD_PTR_ID, rdSave);

    return temp;
}


/******************************************************************************
 * Function:        void MACMemCopyAsync(WORD destAddr, WORD sourceAddr, WORD len)
 *
 * PreCondition:    SPI bus must be initialized (done in MACInit()).
 *
 * Input:           destAddr:   Destination address in the Ethernet memory to
 *                              copy to.  If the MSb is set, the current EWRPT
 *                              value will be used instead.
 *                  sourceAddr: Source address to read from.  If the MSb is
 *                              set, the current ERDPT value will be used
 *                              instead.
 *                  len:        Number of bytes to copy
 *
 * Output:          Byte read from the MRF24W's RAM
 *
 * Side Effects:    None
 *
 * Overview:        Bytes are asynchronously transfered within the buffer.  Call
 *                  MACIsMemCopyDone() to see when the transfer is complete.
 *
 * Note:            If a prior transfer is already in progress prior to
 *                  calling this function, this function will block until it
 *                  can start this transfer.
 *
 *                  If a negative value (bit 15 set) is used for the sourceAddr or destAddr
 *                  parameters, then that pointer will get updated with the
 *                  next address after the read or write.
 *****************************************************************************/
void MACMemCopyAsync(PTR_BASE destAddr, PTR_BASE sourceAddr, WORD len)
{
    UINT16 readSave = 0, writeSave = 0;
    BOOL updateWritePointer;
    BOOL updateReadPointer;
    UINT8 rawScratchId = 0xff;  /* garbage value to avoid compiler warning */
    UINT8 copyBuf[8];
    UINT16 writeIndex, readIndex;
    UINT16 bytesLeft;
    UINT16 origRawIndex;

    if (len == 0)
    {
        return; /* nothing to do */
    } 
    
    EnsureWFisAwake();   
    
    /* if using current location of write pointer */
    if( ((WORD_VAL*)&destAddr)->bits.b15 )
    {
        updateWritePointer = TRUE;
        destAddr = g_encIndex[ENC_WT_PTR_ID]; /* don't need to sync write pointer, should have already been done */
                                              /*  when encIndex was set previously                               */
    }
    /* else use destAddr as write pointer */
    else
    {
        updateWritePointer = FALSE;
        writeSave = g_encIndex[ENC_WT_PTR_ID];
        SyncENCPtrRAWState(ENC_WT_PTR_ID, destAddr);
    }

    /* if using current location of read pointer */
    if( ((WORD_VAL*)&sourceAddr)->bits.b15 )
    {
        updateReadPointer = TRUE;
        sourceAddr = g_encIndex[ENC_RD_PTR_ID]; /* don't need to sync read pointer, should have already been done */
                                                /*  when encIndex was set previously                              */
    }
    /* else use srcAddr as read pointer */
    else
    {
        updateReadPointer = FALSE;
        readSave = g_encIndex[ENC_RD_PTR_ID];
        SyncENCPtrRAWState(ENC_RD_PTR_ID, sourceAddr);
    }
    
    /*-------------------------------------------------*/
    /* If copying from Scratch to Scratch (TCB to TCB) */
    /*-------------------------------------------------*/
    /* This is a special case. We cannot perform a RAW Copy operation within the same RAW window,              */
    /* but we can copy manually data from one section of the scratch to another section of the scratch window. */
    if ((destAddr >= BASE_TCB_ADDR) && (sourceAddr >= BASE_TCB_ADDR) )
    {
        bytesLeft = len;

        /* save the current RAW index in this scratch window */
        origRawIndex = RawGetIndex(RAW_SCRATCH_ID);
        
        /*-------------------------------------------------------------------*/        
        /* If we can safely do a forward copy (from first byte to last byte) */
        /*-------------------------------------------------------------------*/
        if ( ((sourceAddr + len) <= destAddr)   ||  // end of source before dest  (no overlap)
             ((destAddr   + len) <= sourceAddr) ||  // end of dest before source  (no overlap)
              (destAddr < sourceAddr)               // dest before source (overlap, but forward copy safe)              
           )
        {
            /* map read and write indexs from TCB address to Scratch Index */
            readIndex  = sourceAddr - ENC_TCB_BUF_TO_RAW_SCRATCH_BUF_ADJUSTMENT;
            writeIndex = destAddr   - ENC_TCB_BUF_TO_RAW_SCRATCH_BUF_ADJUSTMENT;
            
            while (bytesLeft > 0)
            {
                /* if a full copyBuf worth of bytes to copy */
                if (bytesLeft >= sizeof(copyBuf))
                {
                    /* read a block of bytes from the source and write to destination */
                    RawRead( rawScratchId, readIndex,  sizeof(copyBuf), copyBuf);
                    RawWrite(rawScratchId, writeIndex, sizeof(copyBuf), copyBuf);

                    // index to next block in source and dest
                    readIndex  += sizeof(copyBuf);
                    writeIndex += sizeof(copyBuf);
                    bytesLeft  -= sizeof(copyBuf);
                }
                /* else less than a full copyBuf left to copy */
                else
                {
                    if (bytesLeft > 0)
                    {
                        RawRead( rawScratchId, readIndex,  bytesLeft, copyBuf);
                        RawWrite(rawScratchId, writeIndex, bytesLeft, copyBuf);
                        bytesLeft = 0;
                    }    
                }        
            }    
        } /* end while for foward copy */
        /*---------------------------------------------------------------------------*/
        /* else we need to do a backward copy (from last byte to first byte) because */
        /* start of TCB dest block within TCB src block                              */
        /*---------------------------------------------------------------------------*/        
        else if (destAddr > sourceAddr)
        {
            // map read index from TCB address to Scratch Index
            readIndex  = sourceAddr - ENC_TCB_BUF_TO_RAW_SCRATCH_BUF_ADJUSTMENT + len - 1;
            writeIndex = destAddr   - ENC_TCB_BUF_TO_RAW_SCRATCH_BUF_ADJUSTMENT + len - 1;
            
            while (bytesLeft > 0)
            {
                // if a full copyBuf worth of bytes to copy
                if (bytesLeft >= sizeof(copyBuf))
                {
                    RawRead(rawScratchId,  readIndex  - sizeof(copyBuf) + 1, sizeof(copyBuf), copyBuf);
                    RawWrite(rawScratchId, writeIndex - sizeof(copyBuf) + 1, sizeof(copyBuf), copyBuf);

                    // index to next block in source and dest
                    readIndex  -= sizeof(copyBuf);
                    writeIndex -= sizeof(copyBuf);
                    bytesLeft  -= sizeof(copyBuf);
                }
                // else less than a full copyBuf left to copy
                else
                {
                    if (bytesLeft > 0)
                    {
                        RawRead(rawScratchId, readIndex - bytesLeft + 1, bytesLeft - 1, copyBuf);
                        RawWrite(rawScratchId, writeIndex - bytesLeft + 1, bytesLeft - 1, copyBuf);
                        bytesLeft = 0;
                    }    
                }        
            } // end while    
        }    
        // restore raw index to where it was when this function was called
        RawSetIndex(RAW_SCRATCH_ID, origRawIndex); 

    } 
    /*-------------------------------------------------------------------------------------------*/    
    /* else copying between RAW Data Rx and RAW Data Tx or between Raw Data Tx/Rx and RAW Scratch */
    /*-------------------------------------------------------------------------------------------*/
    else 
    {
        #if defined(WF_DEBUG) /* if asserts enabled */
        /* if stack trying to copy from RAW Tx Data Window to same RAW Tx Data Window */ 
        if (((g_encIndex[ENC_WT_PTR_ID] >= TXSTART) && (g_encIndex[ENC_RD_PTR_ID] >= TXSTART))
                                                    &&
            ((g_encIndex[ENC_WT_PTR_ID] < BASE_TCB_ADDR) && (g_encIndex[ENC_RD_PTR_ID] < BASE_TCB_ADDR)))                                                     
        {
            WF_ASSERT(FALSE);  /* can't copy from within same raw window */
        }
        
        /* if stack trying to copy from RAW Rx Data Window to RAW Rx Data Window */
        if ((g_encIndex[ENC_WT_PTR_ID] < TXSTART) && (g_encIndex[ENC_RD_PTR_ID] < TXSTART))
        {
            WF_ASSERT(FALSE);  /* can't copy from within same raw window */            
        }    
        #endif /* WF_DEBUG */

        /* Copy from source RAW window to destination RAW window.  The indexes in the respective */
        /* RAW windows have been set either in this function or prior to this fucntion call.     */
        RawToRawCopy(g_encPtrRAWId[ENC_WT_PTR_ID], g_encPtrRAWId[ENC_RD_PTR_ID], len);
    }

    if ( !updateReadPointer )
    {
        SyncENCPtrRAWState(ENC_RD_PTR_ID, readSave);
    }

    if ( !updateWritePointer )
    {
        SyncENCPtrRAWState(ENC_WT_PTR_ID, writeSave);
    }
    

} /* end MACMemCopyAsync */


BOOL MACIsMemCopyDone(void)
{
    return TRUE;
}


/******************************************************************************
 * Function:        BYTE MACGet()
 *
 * PreCondition:    SPI bus must be initialized (done in MACInit()).
 *                  ERDPT must point to the place to read from.
 *
 * Input:           None
 *
 * Output:          Byte read from the MRF24W's RAM
 *
 * Side Effects:    None
 *
 * Overview:        MACGet returns the byte pointed to by ERDPT and
 *                  increments ERDPT so MACGet() can be called again.  The
 *                  increment will follow the receive buffer wrapping boundary.
 *
 * Note:            None
 *****************************************************************************/
BYTE MACGet()
{
    BYTE result;

    RawGetByte(g_encPtrRAWId[ENC_RD_PTR_ID], &result, 1);

    g_encIndex[ENC_RD_PTR_ID] += 1;

    return result;
}


/******************************************************************************
 * Function:        WORD MACGetArray(BYTE *val, WORD len)
 *
 * PreCondition:    SPI bus must be initialized (done in MACInit()).
 *                  ERDPT must point to the place to read from.
 *
 * Input:           *val: Pointer to storage location
 *                  len:  Number of bytes to read from the data buffer.
 *
 * Output:          Byte(s) of data read from the data buffer.
 *
 * Side Effects:    None
 *
 * Overview:        Burst reads several sequential bytes from the data buffer
 *                  and places them into local memory.  With SPI burst support,
 *                  it performs much faster than multiple MACGet() calls.
 *                  ERDPT is incremented after each byte, following the same
 *                  rules as MACGet().
 *
 * Note:            None
 *****************************************************************************/
WORD MACGetArray(BYTE *val, WORD len)
{
    WORD i = 0;
    UINT8 byte;


    if ( val )
    {
        RawGetByte(g_encPtrRAWId[ENC_RD_PTR_ID], val, len);
    }
    else
    {
        // Read the data
        while(i<len)
        {
            RawGetByte(g_encPtrRAWId[ENC_RD_PTR_ID], &byte, 1);
            i++;
        }
    }
    g_encIndex[ENC_RD_PTR_ID] += len;

    return len;
}//end MACGetArray


/******************************************************************************
 * Function:        void MACPut(BYTE val)
 *
 * PreCondition:    SPI bus must be initialized (done in MACInit()).
 *                  EWRPT must point to the location to begin writing.
 *
 * Input:           Byte to write into the MRF24W buffer memory
 *
 * Output:          None
 *
 * Side Effects:    None
 *
 * Overview:        MACPut outputs the Write Buffer Memory opcode/constant
 *                  (8 bits) and data to write (8 bits) over the SPI.
 *                  EWRPT is incremented after the write.
 *
 * Note:            None
 *****************************************************************************/
void MACPut(BYTE val)
{
    UINT8 byte = val;

    RawSetByte(g_encPtrRAWId[ENC_WT_PTR_ID], &byte, 1);

    g_encIndex[ENC_WT_PTR_ID] += 1;
}//end MACPut


/******************************************************************************
 * Function:        void MACPutArray(BYTE *val, WORD len)
 *
 * PreCondition:    SPI bus must be initialized (done in MACInit()).
 *                  EWRPT must point to the location to begin writing.
 *
 * Input:           *val: Pointer to source of bytes to copy.
 *                  len:  Number of bytes to write to the data buffer.
 *
 * Output:          None
 *
 * Side Effects:    None
 *
 * Overview:        MACPutArray writes several sequential bytes to the
 *                  MRF24W RAM.  It performs faster than multiple MACPut()
 *                  calls.  EWRPT is incremented by len.
 *
 * Note:            None
 *****************************************************************************/
void MACPutArray(BYTE *val, WORD len)
{
    RawSetByte(g_encPtrRAWId[ENC_WT_PTR_ID], val, len);

    g_encIndex[ENC_WT_PTR_ID] += len;
}//end MACPutArray


/******************************************************************************
 * Function:        void MACPutROMArray(ROM BYTE *val, WORD len)
 *
 * PreCondition:    SPI bus must be initialized (done in MACInit()).
 *                  EWRPT must point to the location to begin writing.
 *
 * Input:           *val: Pointer to source of bytes to copy.
 *                  len:  Number of bytes to write to the data buffer.
 *
 * Output:          None
 *
 * Side Effects:    None
 *
 * Overview:        MACPutArray writes several sequential bytes to the
 *                  MRF24W RAM.  It performs faster than multiple MACPut()
 *                  calls.  EWRPT is incremented by len.
 *
 * Note:            None
 *****************************************************************************/
#if defined(__18CXX)
void MACPutROMArray(ROM BYTE *val, WORD len)
{
    RawSetByteROM(g_encPtrRAWId[ENC_WT_PTR_ID], val, len);

    g_encIndex[ENC_WT_PTR_ID] += len;
}//end MACPutROMArray
#endif


/******************************************************************************
 * Function:        void MACPowerDown(void)
 *
 * PreCondition:    SPI bus must be initialized (done in MACInit()).
 *
 * Input:           None
 *
 * Output:          None
 *
 * Side Effects:    None
 *
 * Overview:        MACPowerDown puts the MRF24W in low power sleep mode. In
 *                  sleep mode, no packets can be transmitted or received.
 *                  All MAC and PHY registers should not be accessed.
 *
 * Note:            If a packet is being transmitted while this function is
 *                  called, this function will block until it is it complete.
 *                  If anything is being received, it will be completed.
 *****************************************************************************/
void MACPowerDown(void)
{
}//end MACPowerDown


/******************************************************************************
 * Function:        void MACPowerUp(void)
 *
 * PreCondition:    SPI bus must be initialized (done in MACInit()).
 *
 * Input:           None
 *
 * Output:          None
 *
 * Side Effects:    None
 *
 * Overview:        MACPowerUp returns the MRF24W back to normal operation
 *                  after a previous call to MACPowerDown().  Calling this
 *                  function when already powered up will have no effect.
 *
 * Note:            If a link partner is present, it will take 10s of
 *                  milliseconds before a new link will be established after
 *                  waking up.  While not linked, packets which are
 *                  transmitted will most likely be lost.  MACIsLinked() can
 *                  be called to determine if a link is established.
 *****************************************************************************/
void MACPowerUp(void)
{
}//end MACPowerUp

#if 0
/* Not needed for MCHP */

void RawSendUntamperedData(UINT8 *pReq, UINT16 len)
{
	BOOL    res;
	UINT8 preambleBuf[2];
	UINT16 byteCount;

    WF_ASSERT(GetTxRawWindowState() != WF_RAW_DATA_MOUNTED);

	// RAW memory alloc
	res = AllocateDataTxBuffer(len);
    WF_ASSERT(res == TRUE);           /* if ever change this need to deallocate Tx buffer */

	/* fill out 2 byte preamble of request message */
	preambleBuf[0] = WF_DATA_REQUEST_TYPE;            // indicate this is a data msg
	preambleBuf[1] = WF_UNTAMPERED_DATA_MSG_SUBTYPE;  // untampered data subtype

    /* write out preamble */
    RawWrite(RAW_TX_ID, 0, sizeof(preambleBuf), preambleBuf);

	// write out payload
	RawSetByte(RAW_TX_ID, (UINT8 *) pReq, len);

	// Instruct WF chip to transmit the packet data in the raw window
	RawSendTxBuffer(len + sizeof(preambleBuf));

}
#endif


/*****************************************************************************
  Function:
	WORD CalcIPBufferChecksum(WORD len)

  Summary:
	Calculates an IP checksum in the MAC buffer itself.

  Description:
	This function calculates an IP checksum over an array of input data 
	existing in the MAC buffer.  The checksum is the 16-bit one's complement 
	of one's complement sum of all words in the data (with zero-padding if 
	an odd number of bytes are summed).  This checksum is defined in RFC 793.

  Precondition:
	TCP is initialized and the MAC buffer pointer is set to the start of
	the buffer.

  Parameters:
	len - number of bytes to be checksummed

  Returns:
	The calculated checksum.

  Remarks:
	All Microchip MACs should perform this function in hardware.
  ***************************************************************************/
extern WORD RawCalculateChecksum(UINT16 length);
WORD CalcIPBufferChecksum(WORD len)
{
    DWORD_VAL Checksum;

    // do checksum calculation via the checksum hardware engine
    Checksum.w[0] = HSTOWFS(RawCalculateChecksum(len));
        
    return Checksum.w[0];
}


#else
/* dummy func to keep C18 compiler happy when module has no executeable code */
void WFMac_EmptyFunc(void)
{
    ;
}
#endif /* WF_CS_TRIS*/
