garyStofer/wifi_wx_station/Firmware/Wifi_Wunder_Station.X/src/APP_cfg.c

#include "APP_cfg.h"
// Used for Wi-Fi assertions
#define WF_MODULE_NUMBER   WF_MODULE_MAIN_DEMO

void
InvalidateAppConfig( void)
{
#if defined(EEPROM_CS_TRIS)
                XEEBeginWrite(0x0000); // Invalidate the EE-prom appconfig
                XEEWrite(0xFF);
                XEEWrite(0xFF);
                XEEEndWrite();
#elif defined(SPIFLASH_CS_TRIS)
                SPIFlashBeginWrite(0x0000);
                SPIFlashWrite(0xFF);
                SPIFlashWrite(0xFF);
#endif
}
APP_CONFIG AppConfig;
static unsigned short wOriginalAppConfigChecksum; // Checksum of the ROM defaults for AppConfig
/*********************************************************************
 * Function:        void InitAppConfig(void)
 *
 * PreCondition:    MPFSInit() is already called.
 *
 * Input:           None
 *
 * Output:          Write/Read non-volatile config variables.
 *
 * Side Effects:    None
 *
 * Overview:        None
 *
 * Note:            None
 ********************************************************************/
// MAC Address Serialization using a MPLAB PM3 Programmer and 
// Serialized Quick Turn Programming (SQTP). 
// The advantage of using SQTP for programming the MAC Address is it
// allows you to auto-increment the MAC address without recompiling 
// the code for each unit.  To use SQTP, the MAC address must be fixed
// at a specific location in program memory.  Uncomment these two pragmas
// that locate the MAC address at 0x1FFF0.  Syntax below is for MPLAB C 
// Compiler for PIC18 MCUs. Syntax will vary for other compilers.
//#pragma romdata MACROM=0x1FFF0
static ROM BYTE SerializedMACAddress[6] = {MY_DEFAULT_MAC_BYTE1, MY_DEFAULT_MAC_BYTE2, MY_DEFAULT_MAC_BYTE3, MY_DEFAULT_MAC_BYTE4, MY_DEFAULT_MAC_BYTE5, MY_DEFAULT_MAC_BYTE6};

void
InitAppConfig(void)
{
#if defined(EEPROM_CS_TRIS) || defined(SPIFLASH_CS_TRIS)
    unsigned char vNeedToSaveDefaults = 0;
#endif

 //   int size = sizeof (NVM_VALIDATION_STRUCT) + sizeof (AppConfig);

    while (1)
    {
        // Start out zeroing all AppConfig bytes to ensure all fields are
        // deterministic for checksum generation
        memset((void*) &AppConfig, 0x00, sizeof (AppConfig));

        AppConfig.Flags.bIsDHCPEnabled = TRUE;
        AppConfig.Flags.bInConfigMode = TRUE;
        memcpypgm2ram((void*) &AppConfig.MyMACAddr, (ROM void*) SerializedMACAddress, sizeof (AppConfig.MyMACAddr));
        //		{
        //			_prog_addressT MACAddressAddress;
        //			MACAddressAddress.next = 0x157F8;
        //			_memcpy_p2d24((char*)&AppConfig.MyMACAddr, MACAddressAddress, sizeof(AppConfig.MyMACAddr));
        //		}
        AppConfig.MyIPAddr.Val = MY_DEFAULT_IP_ADDR_BYTE1 | MY_DEFAULT_IP_ADDR_BYTE2 << 8ul | MY_DEFAULT_IP_ADDR_BYTE3 << 16ul | MY_DEFAULT_IP_ADDR_BYTE4 << 24ul;
        AppConfig.DefaultIPAddr.Val = AppConfig.MyIPAddr.Val;
        AppConfig.MyMask.Val = MY_DEFAULT_MASK_BYTE1 | MY_DEFAULT_MASK_BYTE2 << 8ul | MY_DEFAULT_MASK_BYTE3 << 16ul | MY_DEFAULT_MASK_BYTE4 << 24ul;
        AppConfig.DefaultMask.Val = AppConfig.MyMask.Val;
        AppConfig.MyGateway.Val = MY_DEFAULT_GATE_BYTE1 | MY_DEFAULT_GATE_BYTE2 << 8ul | MY_DEFAULT_GATE_BYTE3 << 16ul | MY_DEFAULT_GATE_BYTE4 << 24ul;
        AppConfig.PrimaryDNSServer.Val = MY_DEFAULT_PRIMARY_DNS_BYTE1 | MY_DEFAULT_PRIMARY_DNS_BYTE2 << 8ul | MY_DEFAULT_PRIMARY_DNS_BYTE3 << 16ul | MY_DEFAULT_PRIMARY_DNS_BYTE4 << 24ul;
        AppConfig.SecondaryDNSServer.Val = MY_DEFAULT_SECONDARY_DNS_BYTE1 | MY_DEFAULT_SECONDARY_DNS_BYTE2 << 8ul | MY_DEFAULT_SECONDARY_DNS_BYTE3 << 16ul | MY_DEFAULT_SECONDARY_DNS_BYTE4 << 24ul;
        // Load the default NetBIOS Host Name
        memcpypgm2ram(AppConfig.NetBIOSName, (ROM void*) MY_DEFAULT_HOST_NAME, 16);
        FormatNetBIOSName(AppConfig.NetBIOSName);

#if defined(WF_CS_TRIS)     // Macro used to decide wether or not there is a WIFI module in the configuration
        // Load the default SSID Name
        WF_ASSERT(sizeof (MY_DEFAULT_SSID_NAME) <= sizeof (AppConfig.MySSID));
        memcpypgm2ram(AppConfig.MySSID, (ROM void*) MY_DEFAULT_SSID_NAME, sizeof (MY_DEFAULT_SSID_NAME));
        AppConfig.SsidLength = sizeof (MY_DEFAULT_SSID_NAME) - 1;

        AppConfig.SecurityMode = MY_DEFAULT_WIFI_SECURITY_MODE;

#if (MY_DEFAULT_WIFI_SECURITY_MODE == WF_SECURITY_OPEN)
        memset(AppConfig.SecurityKey, 0x00, sizeof (AppConfig.SecurityKey));
        AppConfig.SecurityKeyLength = 0;

#elif MY_DEFAULT_WIFI_SECURITY_MODE == WF_SECURITY_WEP_40
        AppConfig.WepKeyIndex = MY_DEFAULT_WEP_KEY_INDEX;
        memcpypgm2ram(AppConfig.SecurityKey, (ROM void*) MY_DEFAULT_WEP_KEYS_40, sizeof (MY_DEFAULT_WEP_KEYS_40) - 1);
        AppConfig.SecurityKeyLength = sizeof (MY_DEFAULT_WEP_KEYS_40) - 1;

#elif MY_DEFAULT_WIFI_SECURITY_MODE == WF_SECURITY_WEP_104
        AppConfig.WepKeyIndex = MY_DEFAULT_WEP_KEY_INDEX;
        memcpypgm2ram(AppConfig.SecurityKey, (ROM void*) MY_DEFAULT_WEP_KEYS_104, sizeof (MY_DEFAULT_WEP_KEYS_104) - 1);
        AppConfig.SecurityKeyLength = sizeof (MY_DEFAULT_WEP_KEYS_104) - 1;

#elif (MY_DEFAULT_WIFI_SECURITY_MODE == WF_SECURITY_WPA_WITH_KEY)       || \
	              (MY_DEFAULT_WIFI_SECURITY_MODE == WF_SECURITY_WPA2_WITH_KEY)      || \
	              (MY_DEFAULT_WIFI_SECURITY_MODE == WF_SECURITY_WPA_AUTO_WITH_KEY)
        memcpypgm2ram(AppConfig.SecurityKey, (ROM void*) MY_DEFAULT_PSK, sizeof (MY_DEFAULT_PSK) - 1);
        AppConfig.SecurityKeyLength = sizeof (MY_DEFAULT_PSK) - 1;

#elif (MY_DEFAULT_WIFI_SECURITY_MODE == WF_SECURITY_WPA_WITH_PASS_PHRASE)     || \
	              (MY_DEFAULT_WIFI_SECURITY_MODE == WF_SECURITY_WPA2_WITH_PASS_PHRASE)    || \
	              (MY_DEFAULT_WIFI_SECURITY_MODE == WF_SECURITY_WPA_AUTO_WITH_PASS_PHRASE)
        memcpypgm2ram(AppConfig.SecurityKey, (ROM void*) MY_DEFAULT_PSK_PHRASE, sizeof (MY_DEFAULT_PSK_PHRASE) - 1);
        AppConfig.SecurityKeyLength = sizeof (MY_DEFAULT_PSK_PHRASE) - 1;
#elif (MY_DEFAULT_WIFI_SECURITY_MODE == WF_SECURITY_WPS_PUSH_BUTTON)
        memset(AppConfig.SecurityKey, 0x00, sizeof (AppConfig.SecurityKey));
        AppConfig.SecurityKeyLength = 0;
#elif (MY_DEFAULT_WIFI_SECURITY_MODE == WF_SECURITY_WPS_PIN)
        memcpypgm2ram(AppConfig.SecurityKey, (ROM void*) MY_DEFAULT_WPS_PIN, sizeof (MY_DEFAULT_WPS_PIN) - 1);
        AppConfig.SecurityKeyLength = sizeof (MY_DEFAULT_WPS_PIN) - 1;
#elif (MY_DEFAULT_WIFI_SECURITY_MODE == WF_SECURITY_EAP)
        memset(AppConfig.SecurityKey, 0x00, sizeof (AppConfig.SecurityKey));
        AppConfig.SecurityKeyLength = 0;
#else 
#error "No security defined"
#endif /* MY_DEFAULT_WIFI_SECURITY_MODE */

#endif // #if defined(WF_CS_TRIS)

        // Compute the checksum of the AppConfig defaults as loaded from ROM
        wOriginalAppConfigChecksum = CalcIPChecksum((BYTE*) & AppConfig, sizeof (AppConfig));

#if defined(EEPROM_CS_TRIS) || defined(SPIFLASH_CS_TRIS)
        {
            NVM_VALIDATION_STRUCT NVMValidationStruct;

            // Check to see if we have a flag set indicating that we need to
            // save the ROM default AppConfig values.
            if (vNeedToSaveDefaults)
                SaveAppConfig(&AppConfig);

            // Read the NVMValidation record and AppConfig struct out of EEPROM/Flash
#if defined(EEPROM_CS_TRIS)
            {
                XEEReadArray(0x0000, (BYTE*) & NVMValidationStruct, sizeof (NVMValidationStruct));
                XEEReadArray(sizeof (NVMValidationStruct), (BYTE*) & AppConfig, sizeof (AppConfig));
            }
#elif defined(SPIFLASH_CS_TRIS)
            {
                SPIFlashReadArray(0x0000, (BYTE*) & NVMValidationStruct, sizeof (NVMValidationStruct));
                SPIFlashReadArray(sizeof (NVMValidationStruct), (BYTE*) & AppConfig, sizeof (AppConfig));
            }
#endif

            // Check EEPROM/Flash validitity.  If it isn't valid, set a flag so
            // that we will save the ROM default values on the next loop
            // iteration.
            if ((NVMValidationStruct.wConfigurationLength != sizeof (AppConfig)) ||
                    (NVMValidationStruct.wOriginalChecksum != wOriginalAppConfigChecksum) ||
                    (NVMValidationStruct.wCurrentChecksum != CalcIPChecksum((BYTE*) & AppConfig, sizeof (AppConfig))))
            {
                // Check to ensure that the vNeedToSaveDefaults flag is zero,
                // indicating that this is the first iteration through the do
                // loop.  If we have already saved the defaults once and the
                // EEPROM/Flash still doesn't pass the validity check, then it
                // means we aren't successfully reading or writing to the
                // EEPROM/Flash.  This means you have a hardware error and/or
                // SPI configuration error.
                if (vNeedToSaveDefaults)
                {
                    while (1);
                }

                // Set flag and restart loop to load ROM defaults and save them
                vNeedToSaveDefaults = 1;
                continue;
            }

            // If we get down here, it means the EEPROM/Flash has valid contents
            // and either matches the ROM defaults or previously matched and
            // was run-time reconfigured by the user.  In this case, we shall
            // use the contents loaded from EEPROM/Flash.
            break;
        }
#endif
        break;
    }
}

#if defined(EEPROM_CS_TRIS) || defined(SPIFLASH_CS_TRIS)

void
SaveAppConfig(const APP_CONFIG *ptrAppConfig)
{
    NVM_VALIDATION_STRUCT NVMValidationStruct;

    // Ensure adequate space has been reserved in non-volatile storage to
    // store the entire AppConfig structure.  If you get stuck in this while(1)
    // trap, it means you have a design time misconfiguration in TCPIPConfig.h.
    // You must increase MPFS_RESERVE_BLOCK to allocate more space.
#if defined(STACK_USE_MPFS2)
    if (sizeof (NVM_VALIDATION_STRUCT) + sizeof (APP_CONFIG) > MPFS_RESERVE_BLOCK)
    {

        putrsUART((ROM char*) "MPFS_RESERVE_BLOCK too small!");

        while (1);
    }
#endif

    // Get proper values for the validation structure indicating that we can use
    // these EEPROM/Flash contents on future boot ups
    NVMValidationStruct.wOriginalChecksum = wOriginalAppConfigChecksum;
    NVMValidationStruct.wCurrentChecksum = CalcIPChecksum((BYTE*) ptrAppConfig, sizeof (APP_CONFIG));
    NVMValidationStruct.wConfigurationLength = sizeof (APP_CONFIG);

    // Write the validation struct and current AppConfig contents to EEPROM/Flash
#if defined(EEPROM_CS_TRIS)
    XEEBeginWrite(0x0000);
    XEEWriteArray((BYTE*) & NVMValidationStruct, sizeof (NVMValidationStruct));
    XEEWriteArray((BYTE*) ptrAppConfig, sizeof (APP_CONFIG));
    XEEEndWrite();
#else
    SPIFlashBeginWrite(0x0000);
    SPIFlashWriteArray((BYTE*) & NVMValidationStruct, sizeof (NVMValidationStruct));
    SPIFlashWriteArray((BYTE*) ptrAppConfig, sizeof (APP_CONFIG));
#endif
}

#endif
