garyStofer/wifi_wx_station/Firmware/Wifi_Wunder_Station.X/src/WF_Config.c

/******************************************************************************

 MRF24W Driver Customization
 Module for Microchip TCP/IP Stack
  -Provides access to MRF24W WiFi controller
  -Reference: MRF24W Data sheet, IEEE 802.11 Standard

*******************************************************************************
 FileName:		WF_Config.c
 Dependencies:	TCP/IP Stack header files
 Processor:		PIC18, PIC24F, PIC24H, dsPIC30F, dsPIC33F, PIC32
 Compiler:		Microchip C32 v1.10b or higher
				Microchip C30 v3.22 or higher
				Microchip C18 v3.34 or higher
 Company:		Microchip Technology, Inc.

 Software License Agreement

 Copyright (C) 2002-2010 Microchip Technology Inc.  All rights reserved.

 Microchip licenses to you the right to use, modify, copy, and distribute:
 (i)  the Software when embedded on a Microchip microcontroller or digital 
      signal controller product ("Device") which is integrated into 
      Licensee's product; or
 (ii) ONLY the Software driver source files ENC28J60.c, ENC28J60.h,
      ENCX24J600.c and ENCX24J600.h ported to a non-Microchip device used in 
	  conjunction with a Microchip ethernet controller for the sole purpose 
	  of interfacing with the ethernet controller.

 You should refer to the license agreement accompanying this Software for 
 additional information regarding your rights and obligations.

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

 Author				Date		Comment
~~~~~~~~~~~~~~~~~~~~~~~~~~~~~~~~~~~~~~~~~~~~~~~~~~~~~~~~~~~~~~~~~~~~~~~~~~~~~~~
 KH                 27 Jan 2010 Created for MRF24W
******************************************************************************/


#include "HardwareProfile.h"

#if defined(WF_CS_TRIS)

/*==========================================================================*/
/*                                  INCLUDES                                */
/*==========================================================================*/
#include "TCPIP Stack/TCPIP.h"

#if defined ( EZ_CONFIG_SCAN )
#include "TCPIP Stack/WFEasyConfig.h"
#endif /* EZ_CONFIG_SCAN */


/*==========================================================================*/
/*                                  DEFINES                                 */
/*==========================================================================*/

/* used for assertions */
#if defined(WF_DEBUG)
    #define WF_MODULE_NUMBER    WF_MODULE_WF_CONFIG
#endif


#if defined(STACK_USE_DHCP_CLIENT)
void RenewDhcp(void);
#endif

extern BOOL GetAppPowerSaveMode(void);
extern void ReenablePowerSaveMode(void);


/*****************************************************************************
 * FUNCTION: WF_ProcessEvent
 *
 * RETURNS:  None
 *
 * PARAMS:   event      -- event that occurred
 *           eventInfo  -- additional information about the event.  Not all events
 *                         have associated info, in which case this value will be
 *                         set to WF_NO_ADDITIONAL_INFO (0xff)
 *           extraInfo - more additional information about the event
 *
 *  NOTES:   The Host application must NOT directly call this function.  This 
 *           function is called by the WiFi Driver code when an event occurs
 *           that may need processing by the Host CPU.  
 *
 *           No other WiFi Driver function should be called from this function, with the
 *           exception of WF_ASSERT.  It is recommended that if the application wishes to be 
 *           notified of an event that it simply set a flag and let application code in the 
 *           main loop handle the event.  
 *
 *           WFSetFuncState must be called when entering and leaving this function.  
 *           When WF_DEBUG is enabled this allows a runtime check if any illegal WF functions 
 *           are called from within this function.
 *
 *           For events that the application is not interested in simply leave the
 *           case statement empty.
  *
 *           Customize this function as needed for your application.
 *****************************************************************************/
short g_isPSK_Ready;
void WF_ProcessEvent(UINT8 event, UINT16 eventInfo, UINT8 *extraInfo)
{

    char buf[8];

    /* this function tells the WF driver that we are in this function */
    WFSetFuncState(WF_PROCESS_EVENT_FUNC, WF_ENTERING_FUNCTION);
      
    switch (event)
    {
        /*--------------------------------------*/
        case WF_EVENT_CONNECTION_SUCCESSFUL:
        /*--------------------------------------*/   
            putrsUART("WiFi Connection Successful\r\n");
            if ( g_isPSK_Ready == -1)       // mark that encryption is complete if it was requested
                    g_isPSK_Ready = 1;
            break;
        
        /*--------------------------------------*/            
        case WF_EVENT_CONNECTION_FAILED:
        case WF_EVENT_CONNECTION_TEMPORARILY_LOST:
        case WF_EVENT_CONNECTION_PERMANENTLY_LOST:            
        /*--------------------------------------*/
         
            WF_OutputConnectionDebugMsg(event, eventInfo);

            break;

        /*--------------------------------------*/    
        case WF_EVENT_CONNECTION_REESTABLISHED:
        /*--------------------------------------*/

            putrsUART("WiFi Connection Reestablished\r\n");

            break;
            
        /*--------------------------------------*/
        case WF_EVENT_SCAN_RESULTS_READY:
        /*--------------------------------------*/  
     
            putrsUART("Event: Scan Results Ready,");
            sprintf(buf, " %d", eventInfo);
            putsUART(buf);
            putrsUART("results\r\n");
       

            #if defined ( EZ_CONFIG_SCAN ) && !defined(__18CXX)
            WFScanEventHandler(eventInfo);
			#endif /* EZ_CONFIG_SCAN */
            break;
			
        case WF_EVENT_KEY_CALCULATION_REQUEST:
            putrsUART("WiFi Key Calculation Even\r\n");
	    break;
		
        default:
            WF_ASSERT(FALSE);  /* unknown event */
            break;
    }        
    
    /* Informs the WF driver that we are leaving this function */
    WFSetFuncState(WF_PROCESS_EVENT_FUNC, WF_LEAVING_FUNCTION);
}    

// Global variables
UINT8 ConnectionProfileID;

/*****************************************************************************
 * FUNCTION: WF_Connect
 *
 * RETURNS:  None
 *
 * PARAMS:   None
 *
 *  NOTES:   Connects to an 802.11 network.  Customize this function as needed
 *           for your application.
 *****************************************************************************/
void
WF_Connect(int Retry_count)
{
    UINT8 channelList[] = MY_DEFAULT_CHANNEL_LIST;

    /* create a Connection Profile */
    WF_CPCreate(&ConnectionProfileID);
    WF_SetRegionalDomain(MY_DEFAULT_DOMAIN);

    WF_CPSetSsid(ConnectionProfileID,
            AppConfig.MySSID,
            AppConfig.SsidLength);

    WF_CPSetNetworkType(ConnectionProfileID, MY_DEFAULT_NETWORK_TYPE);
    WF_CASetScanType(MY_DEFAULT_SCAN_TYPE);
    WF_CASetChannelList(channelList, sizeof (channelList));

    // The Retry Count parameter tells the WiFi Connection manager how many attempts to make when trying
    // to connect to an existing network.  In the Infrastructure case, the default is to retry forever so that
    // if the AP is turned off or out of range, the radio will continue to attempt a connection until the
    // AP is eventually back on or in range.  In the Adhoc case, the default is to retry 3 times since the
    // purpose of attempting to establish a network in the Adhoc case is only to verify that one does not
    // initially exist.  If the retry count was set to WF_RETRY_FOREVER in the AdHoc mode, an AdHoc network
    // would never be established.
    WF_CASetListRetryCount(Retry_count);
    WF_CASetEventNotificationAction(MY_DEFAULT_EVENT_NOTIFICATION_LIST);
    WF_CASetBeaconTimeout(MY_DEFAULT_BEACON_TIMEOUT);

#if defined(MRF24WG)

    if (gRFModuleVer1209orLater)
    {
        // If WEP security is used, set WEP Key Type.  The default WEP Key Type is Shared Key.
        if (AppConfig.SecurityMode == WF_SECURITY_WEP_40 || AppConfig.SecurityMode == WF_SECURITY_WEP_104)
        {
            WF_CPSetWepKeyType(ConnectionProfileID, MY_DEFAULT_WIFI_SECURITY_WEP_KEYTYPE);
        }
    }
    // Error check items specific to WPS Push Button mode
#if (MY_DEFAULT_WIFI_SECURITY_MODE==WF_SECURITY_WPS_PUSH_BUTTON)
#if !defined(WF_P2P)
    WF_ASSERT(strlen(AppConfig.MySSID) == 0); // SSID must be empty when using WPS
    WF_ASSERT(sizeof (channelList) == 11); // must scan all channels for WPS
#endif

#if (MY_DEFAULT_NETWORK_TYPE == WF_P2P)
    WF_ASSERT(strcmp((char *) AppConfig.MySSID, "DIRECT-") == 0);
    WF_ASSERT(sizeof (channelList) == 3);
    WF_ASSERT(channelList[0] == 1);
    WF_ASSERT(channelList[1] == 6);
    WF_ASSERT(channelList[2] == 11);
#endif
#endif

#endif /* MRF24WG */

    WF_CPSetSecurity(ConnectionProfileID,
            AppConfig.SecurityMode,
            AppConfig.WepKeyIndex, /* only used if WEP enabled */
            AppConfig.SecurityKey,
            AppConfig.SecurityKeyLength);

#if MY_DEFAULT_PS_POLL == WF_ENABLED
    WF_PsPollEnable(TRUE);
#if !defined(MRF24WG)
    if (gRFModuleVer1209orLater)
        WFEnableDeferredPowerSave();
#endif	/* !defined(MRF24WG) */
#else	/* MY_DEFAULT_PS_POLL != WF_ENABLED */
    WF_PsPollDisable();
#endif	/* MY_DEFAULT_PS_POLL == WF_ENABLED */

#ifdef WF_AGGRESSIVE_PS
#if !defined(MRF24WG)
    if (gRFModuleVer1209orLater)
        WFEnableAggressivePowerSave();
#endif
#endif


    WF_OutputConnectionInfo(&AppConfig);


#if defined(DISABLE_MODULE_FW_CONNECT_MANAGER_IN_INFRASTRUCTURE)
    WF_DisableModuleConnectionManager();
#endif

#if defined(MRF24WG)
    WFEnableDebugPrint(ENABLE_WPS_PRINTS | ENABLE_P2P_PRINTS);
#endif
    WF_CMConnect(ConnectionProfileID);
}
#endif /* WF_CS_TRIS */
