garyStofer/wifi_wx_station/PC_Tools/C++/WX_Boostrap/Win_formtest/Form_main.cpp

// Win_formtest.cpp : main project file.
// $Id$
#include "stdafx.h"
#include "Form1.h"

using namespace Win_formtest;

[STAThreadAttribute]
int main(array<System::String ^> ^args)
{
	// Enabling Windows XP visual effects before any controls are created
	Application::EnableVisualStyles();
	Application::SetCompatibleTextRenderingDefault(false); 

	// Create the main window and run it
	Application::Run(gcnew Form1());
	return 0;
}
