garyStofer/wifi_wx_station/PC_Tools/C++/WX_Boostrap/Win_formtest/stdafx.cpp

// stdafx.cpp : source file that includes just the standard includes
// Win_formtest.pch will be the pre-compiled header
// stdafx.obj will contain the pre-compiled type information

#include "stdafx.h"
