garyStofer/wifi_wx_station/PC_Tools/C++/WX_Boostrap/Win_formtest/stdafx.h

// stdafx.h : include file for standard system include files,
// or project specific include files that are used frequently, but
// are changed infrequently
#pragma once

// TODO: reference additional headers your program requires here
#include "windows.h"
#include "CP210xManufacturingDLL.h"
#include "CP210xRuntimeDLL.h"
#include "string"
